thpoll83/PolyKybd/RoHS/PolyKybd-PCB-Layers.pdf

# PolyKybd Split72

## PCB Layer Documentation — Rev 3.2

Fabrication layer plots for the left and right boards (4-layer PCB), generated from the released production Gerber set.

### Prepared: 2026-07-13

PolyKybd — CE Technical File | PCB Layer Documentation
PCB Layer Documentation | Page 1

# Contents

## Left board (182.1 x 129.1 mm)

Top Copper — F.Cu p.4
Inner Layer 1 — In1.Cu p.5
Inner Layer 2 — In2.Cu p.6
Bottom Copper — B.Cu p.7
Top Solder Mask — F.Mask p.8 Bottom Solder Mask — B.Mask p.9 Top Paste — F.Paste p.10
Bottom Paste — B.Paste p.11
Board Outline — Edge.Cuts p.12

## Right board (182.1 x 129.1 mm)

Top Copper — F.Cu p.13
Inner Layer 1 — In1.Cu p.14
Inner Layer 2 — In2.Cu p.15
Bottom Copper — B.Cu p.16
Top Solder Mask — F.Mask p.17 Bottom Solder Mask — B.Mask p.18 Top Paste — F.Paste p.19
Bottom Paste — B.Paste p.20 Board Outline — Edge.Cuts p.21

# PCB construction summary

Layer count: 4 (2 outer + 2 inner copper). Stack order top->bottom: F.Cu, In1.Cu, In2.Cu, B.Cu. Base material: FR-4. Surface finish: ENIG or lead-free HASL (per PCB fabricator RoHS certificate). Left board outline: 182.1 x 129.1 mm.
Right board outline: 182.1 x 129.1 mm.

Layers shown: copper (x4), solder mask (top/bottom), solder paste (top/bottom), board outline. Silkscreen layers are part of the released Gerber set; export from KiCad (kicad-cli) if required.
Confirm exact dielectric thicknesses / copper weights with the PCB fabricator.

# Left board — Top Copper — F.Cu

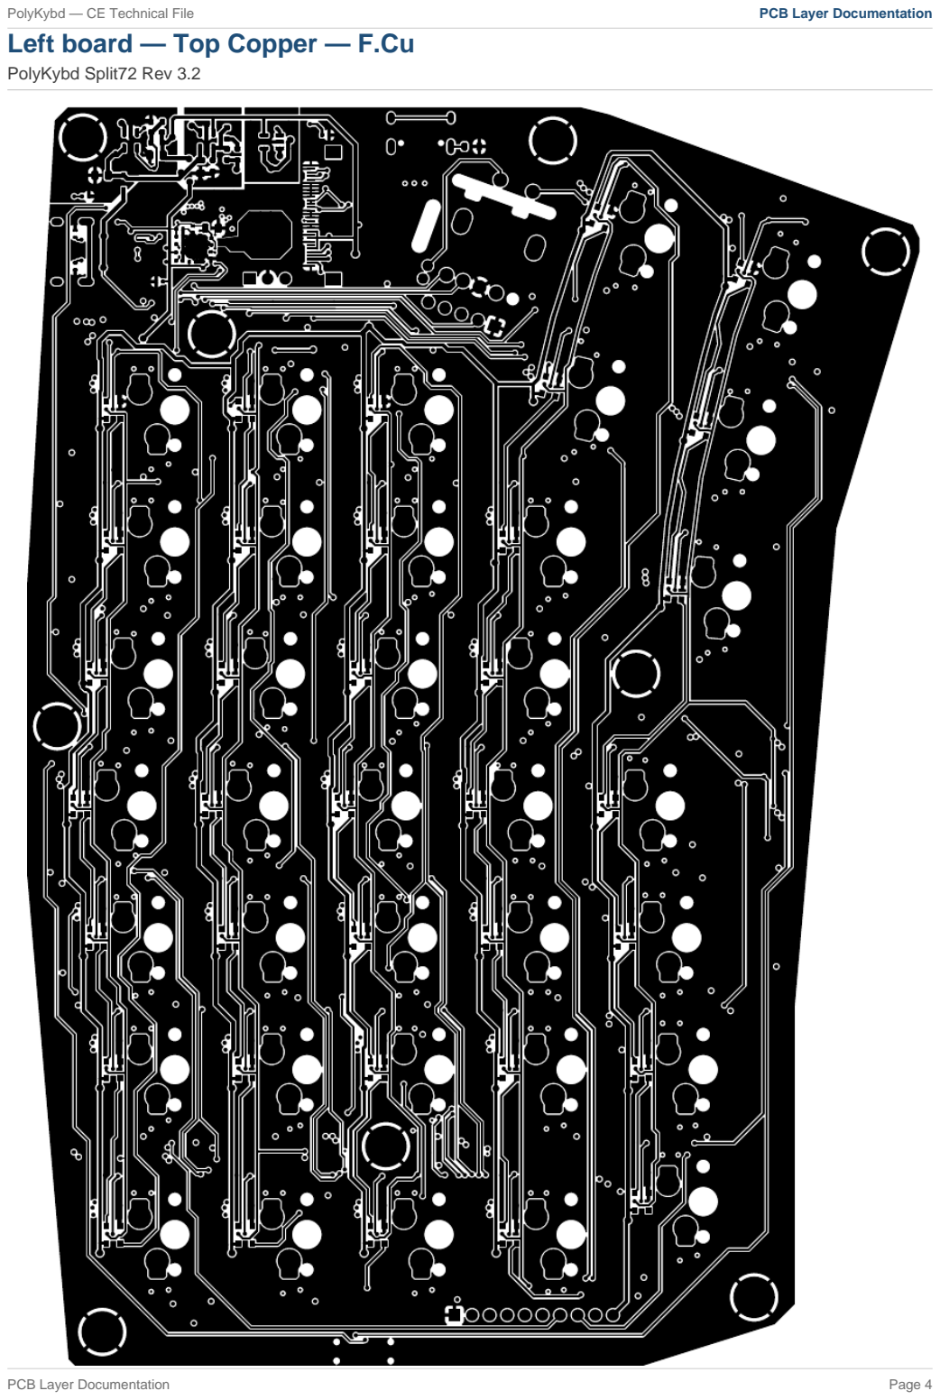
[picture p49: page 4]

### PolyKybd Split72 Rev 3.2

# Left board — Inner Layer 1 — In1.Cu

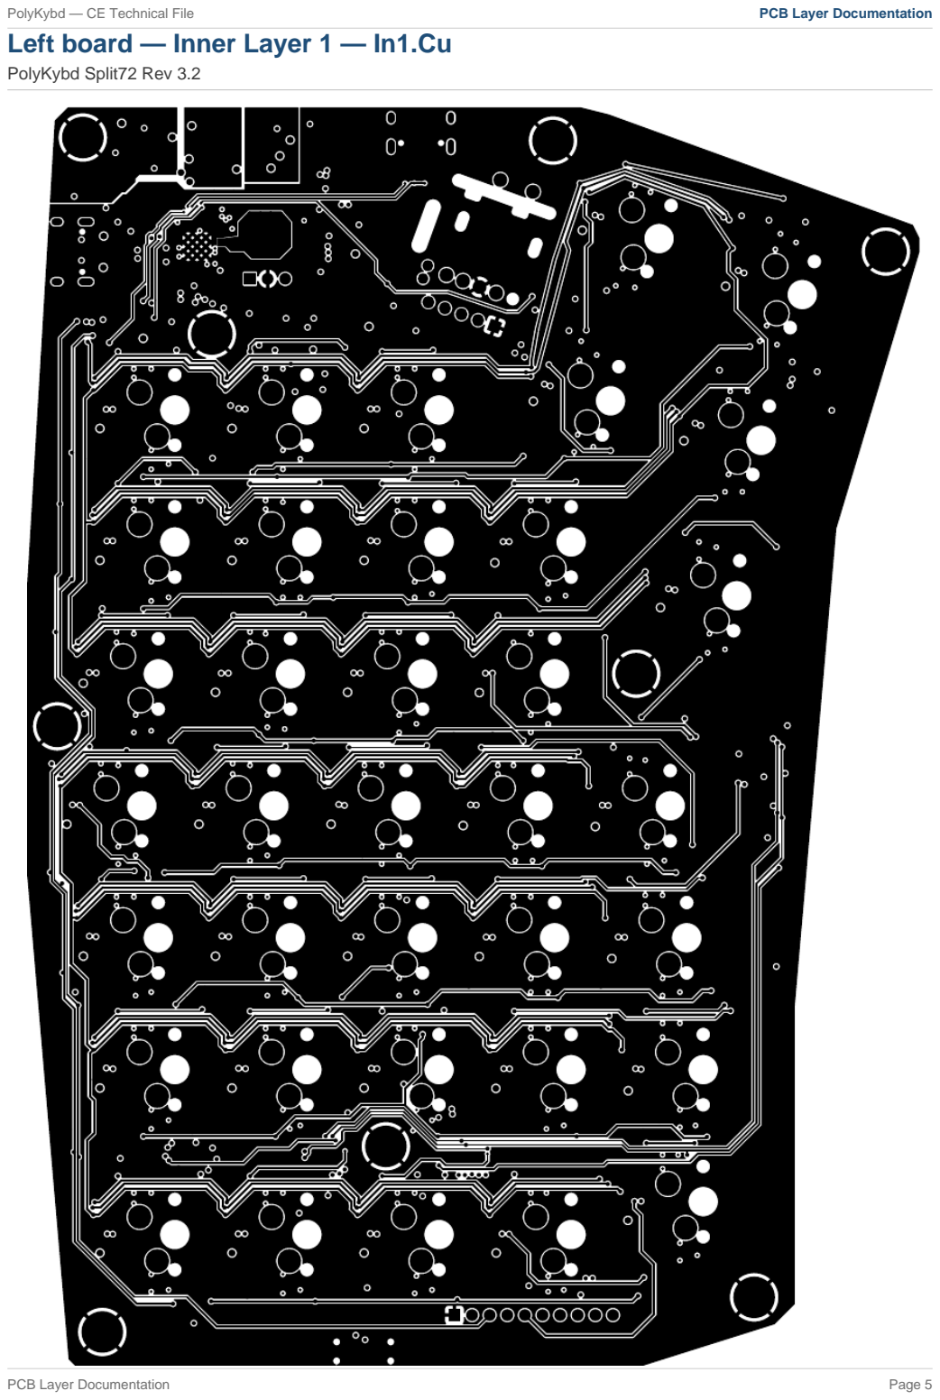
[picture p50: page 5]

# Left board — Inner Layer 2 — In2.Cu

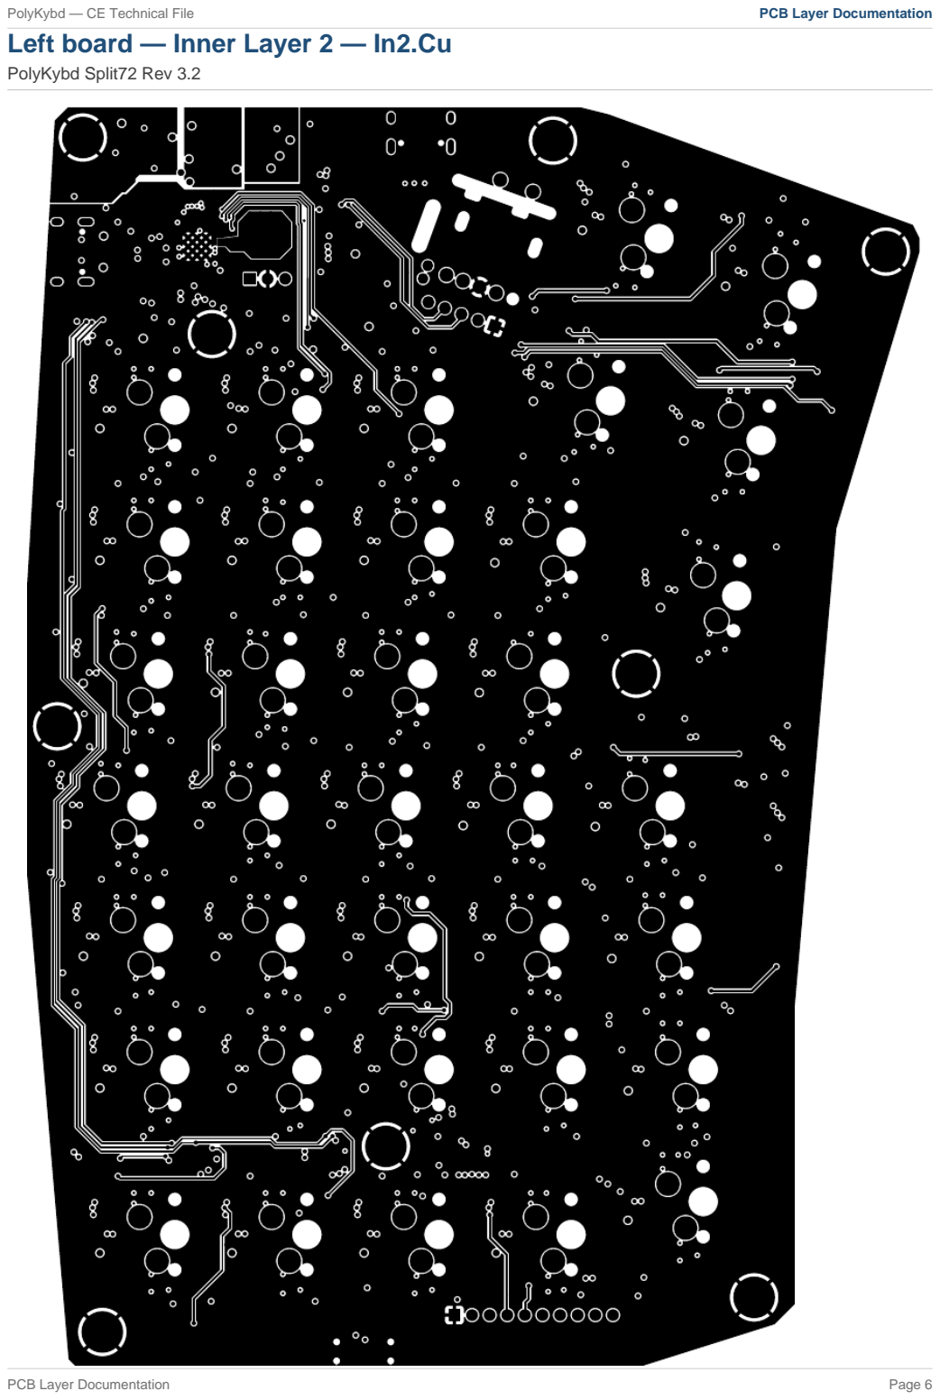
[picture p51: page 6]

# Left board — Bottom Copper — B.Cu

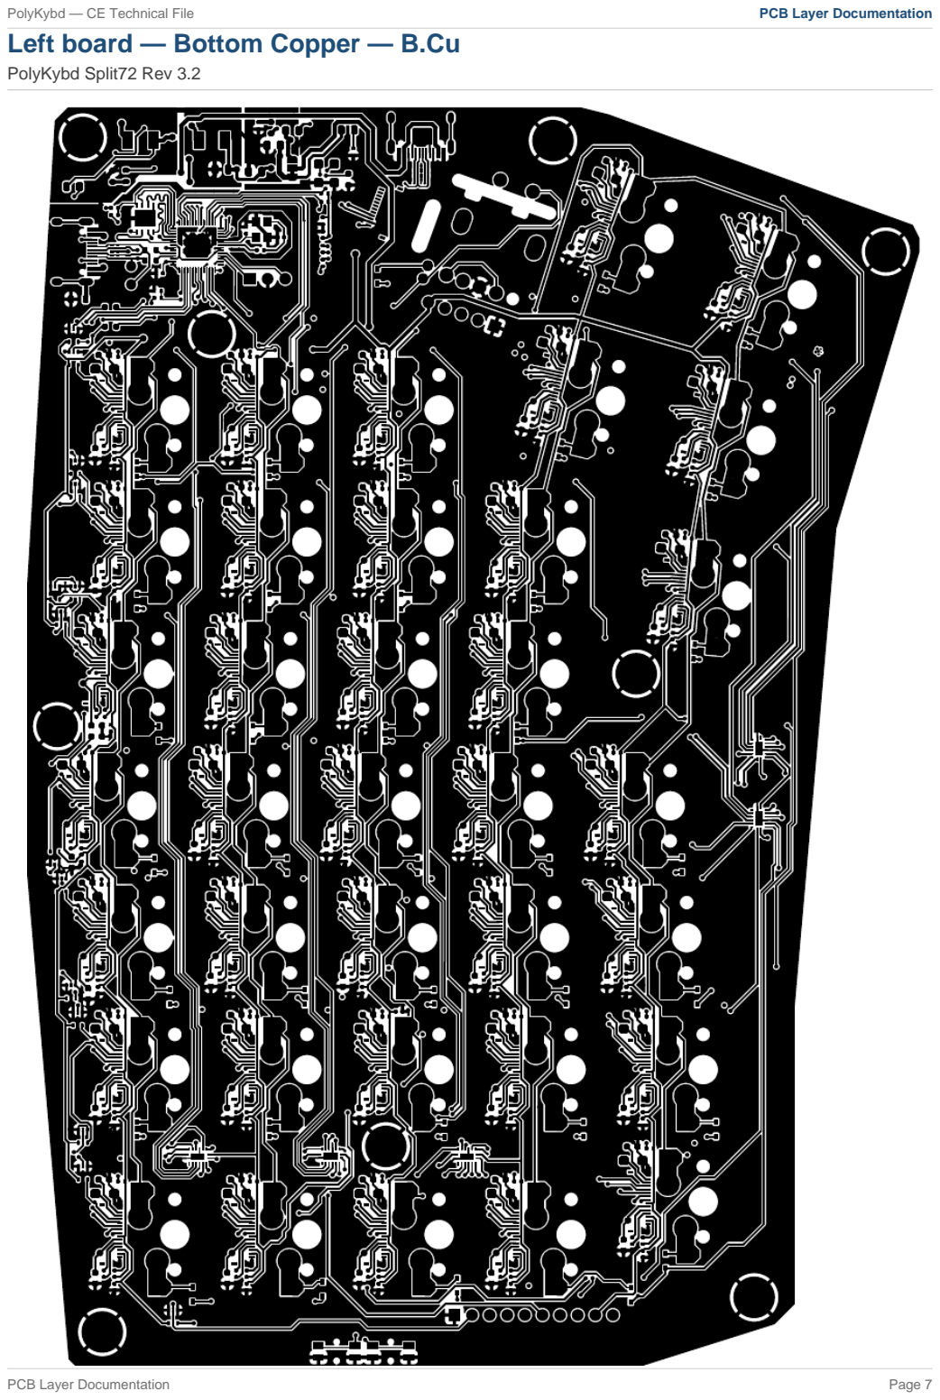
[picture p52: page 7]

# Left board — Top Solder Mask — F.Mask

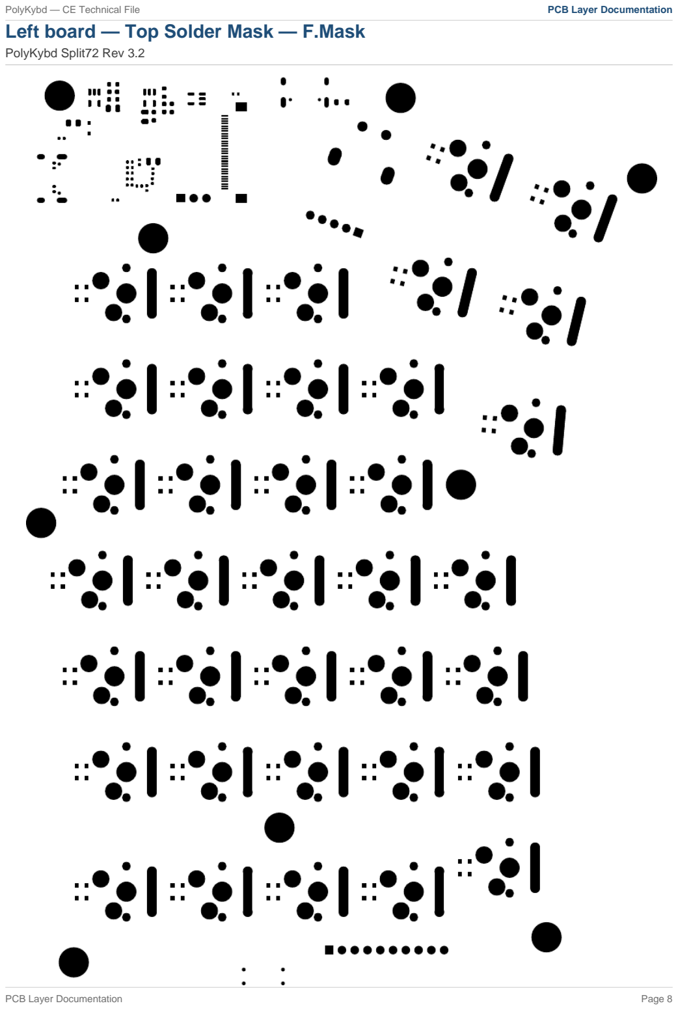
[picture p53: page 8]

# Left board — Bottom Solder Mask — B.Mask

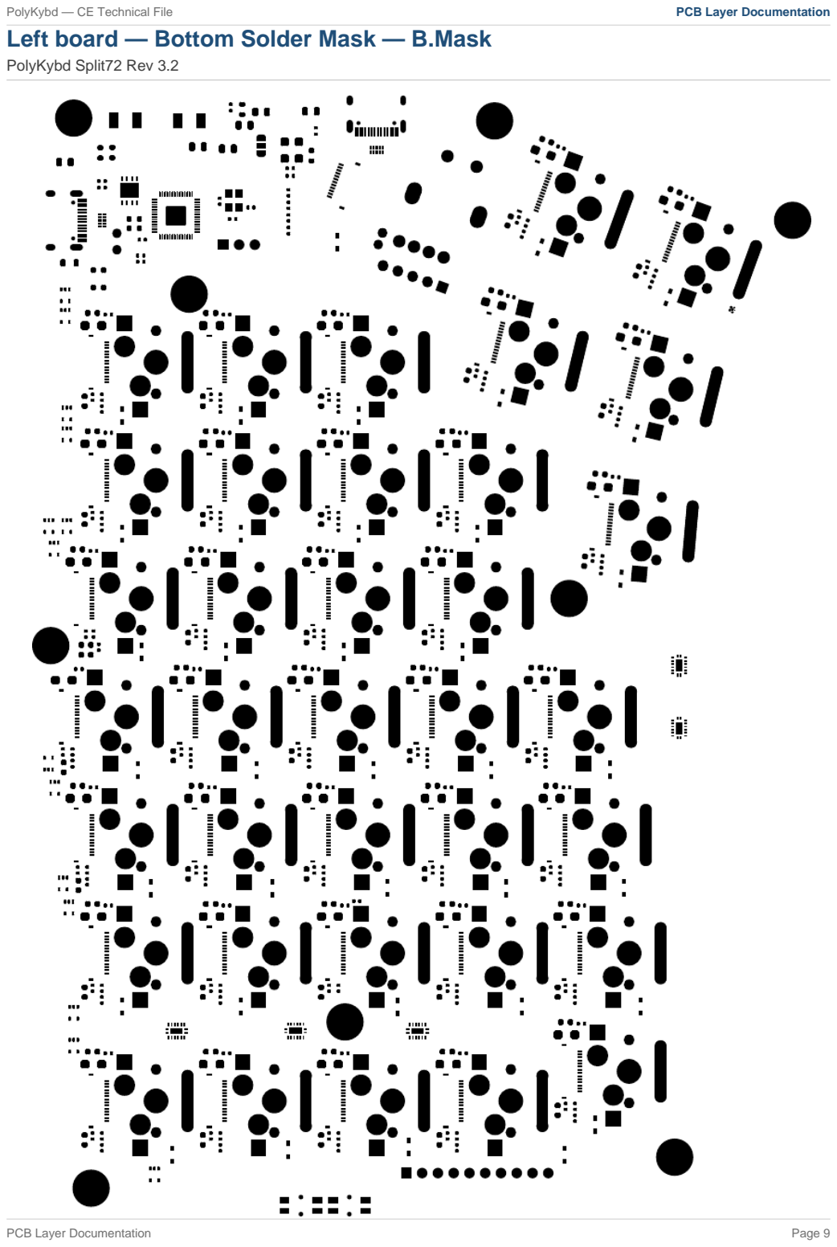
[picture p54: page 9]

# Left board — Top Paste — F.Paste

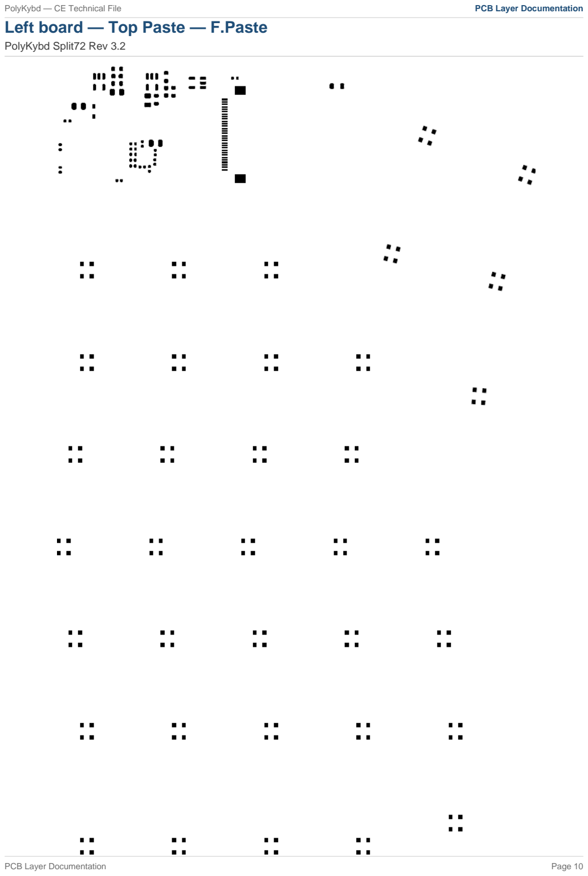
[picture p55: page 10]

# Left board — Bottom Paste — B.Paste

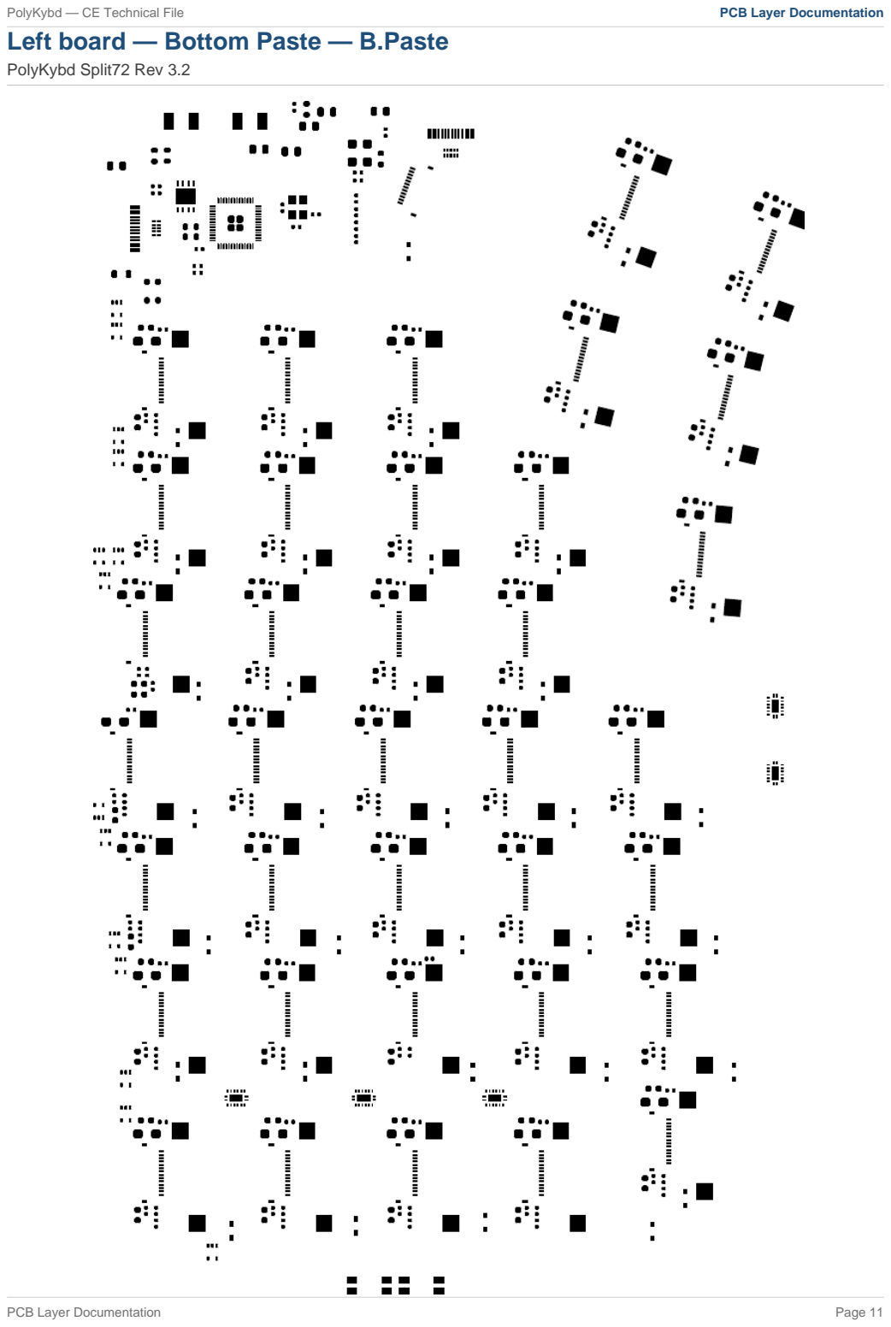
[picture p56: page 11]

# Left board — Board Outline — Edge.Cuts

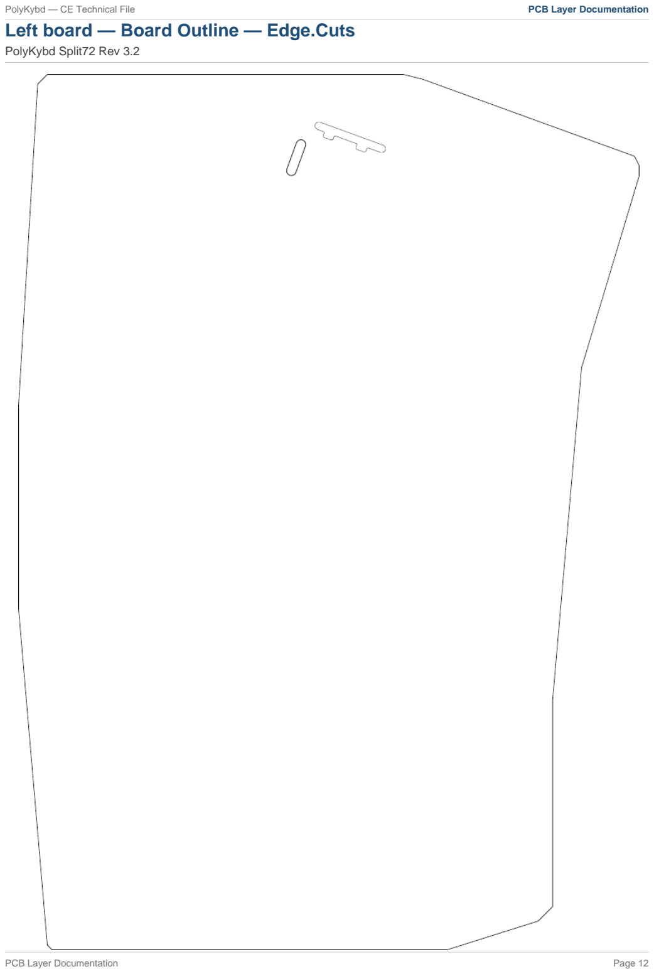
[picture p57: page 12]

# Right board — Top Copper — F.Cu

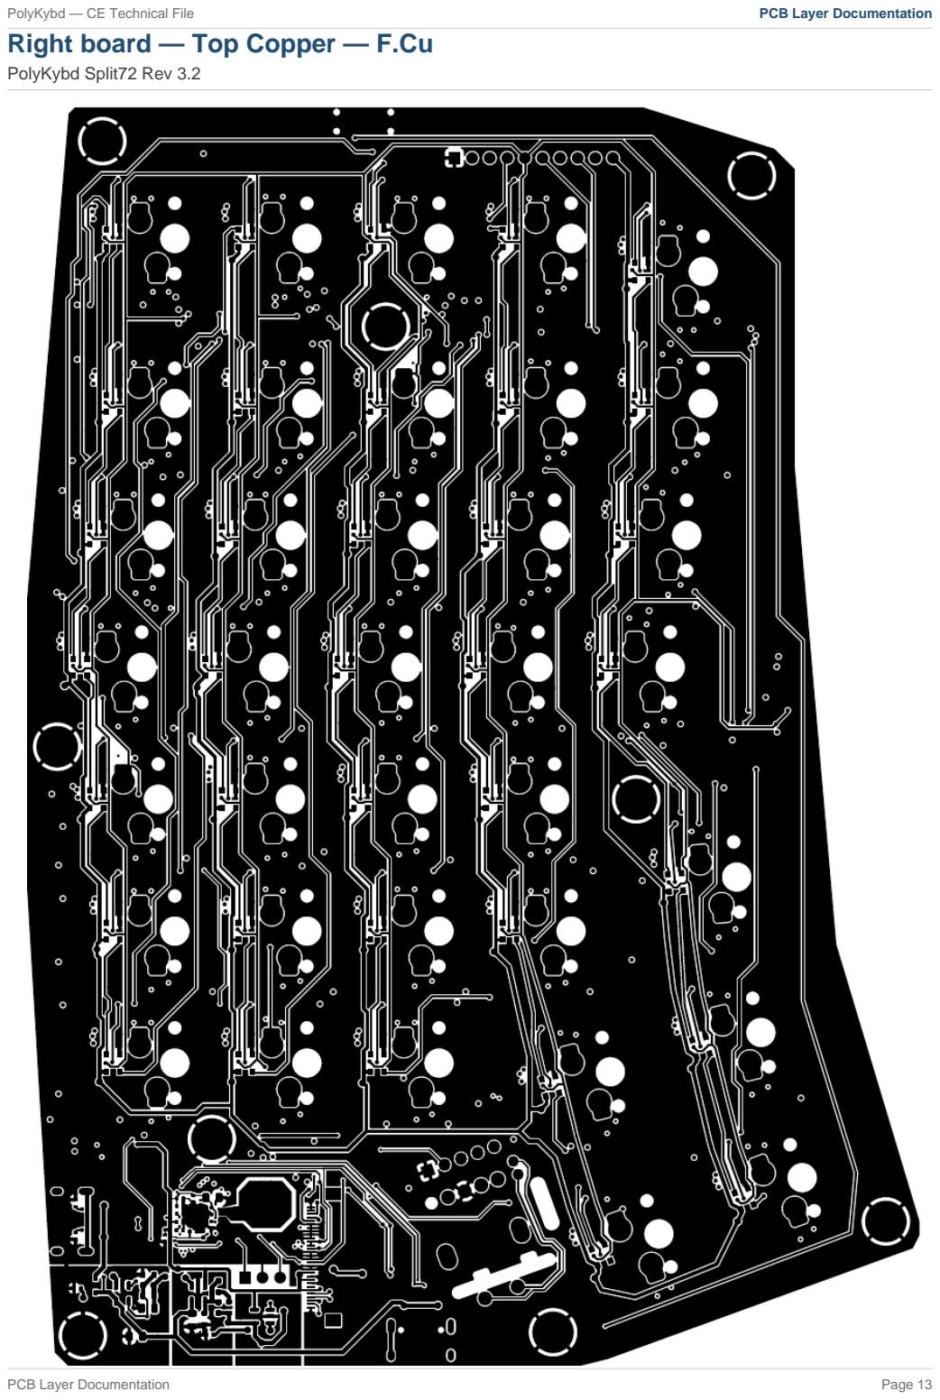
[picture p58: page 13]

# Right board — Inner Layer 1 — In1.Cu

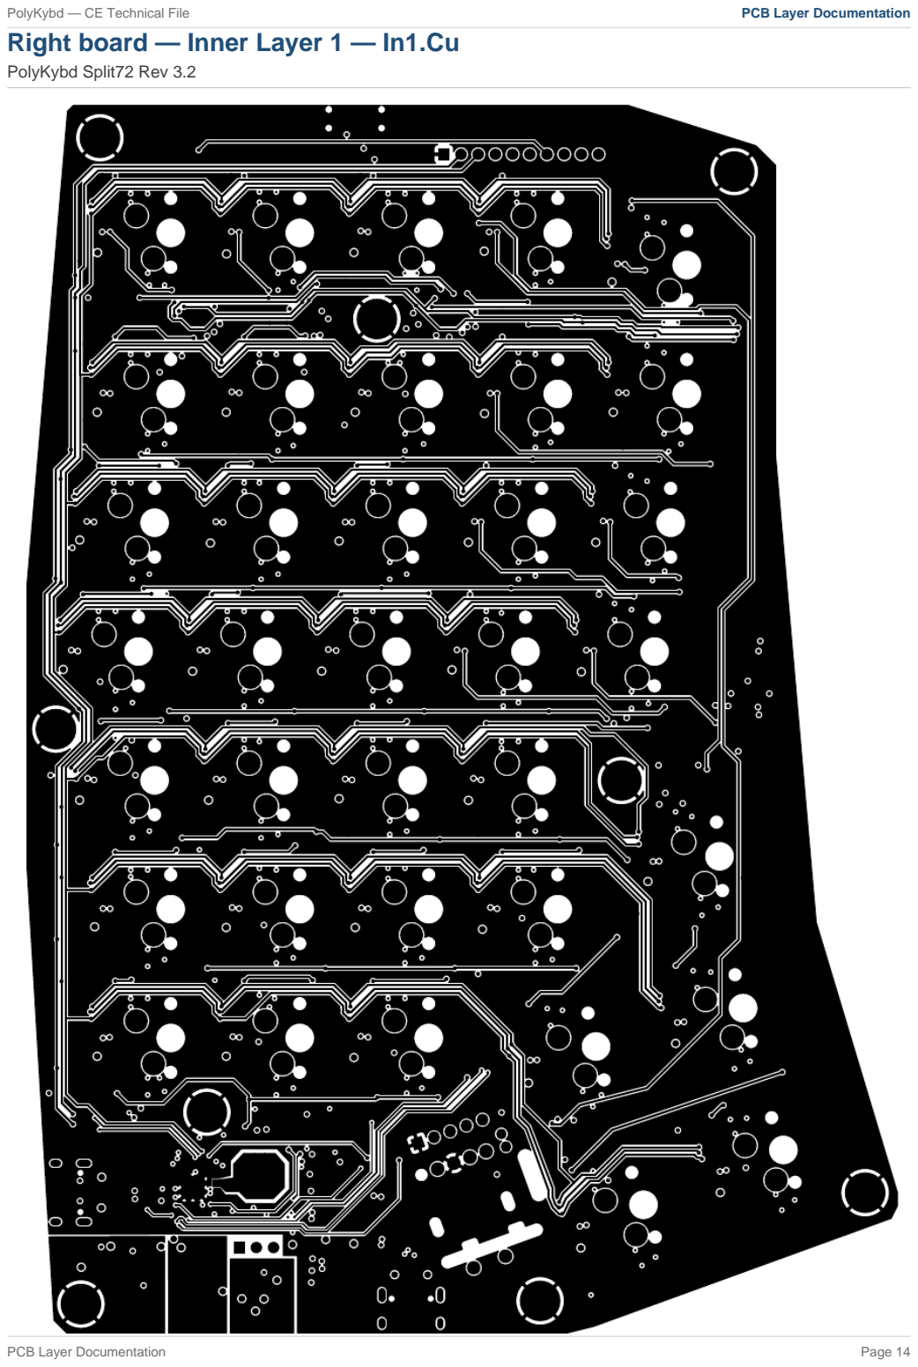
[picture p59: page 14]

# Right board — Inner Layer 2 — In2.Cu

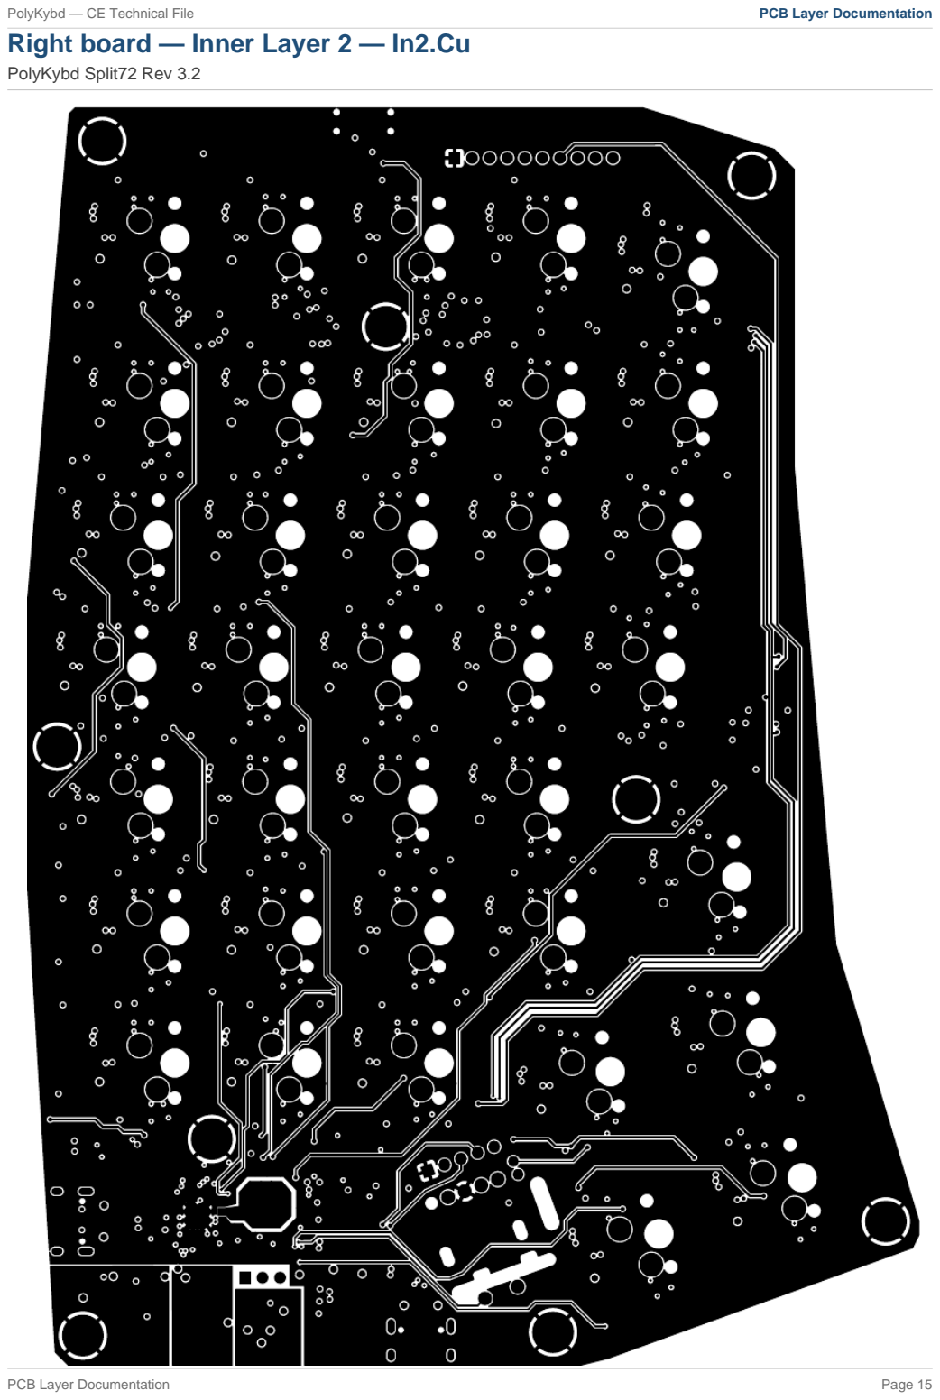
[picture p60: page 15]

# Right board — Bottom Copper — B.Cu

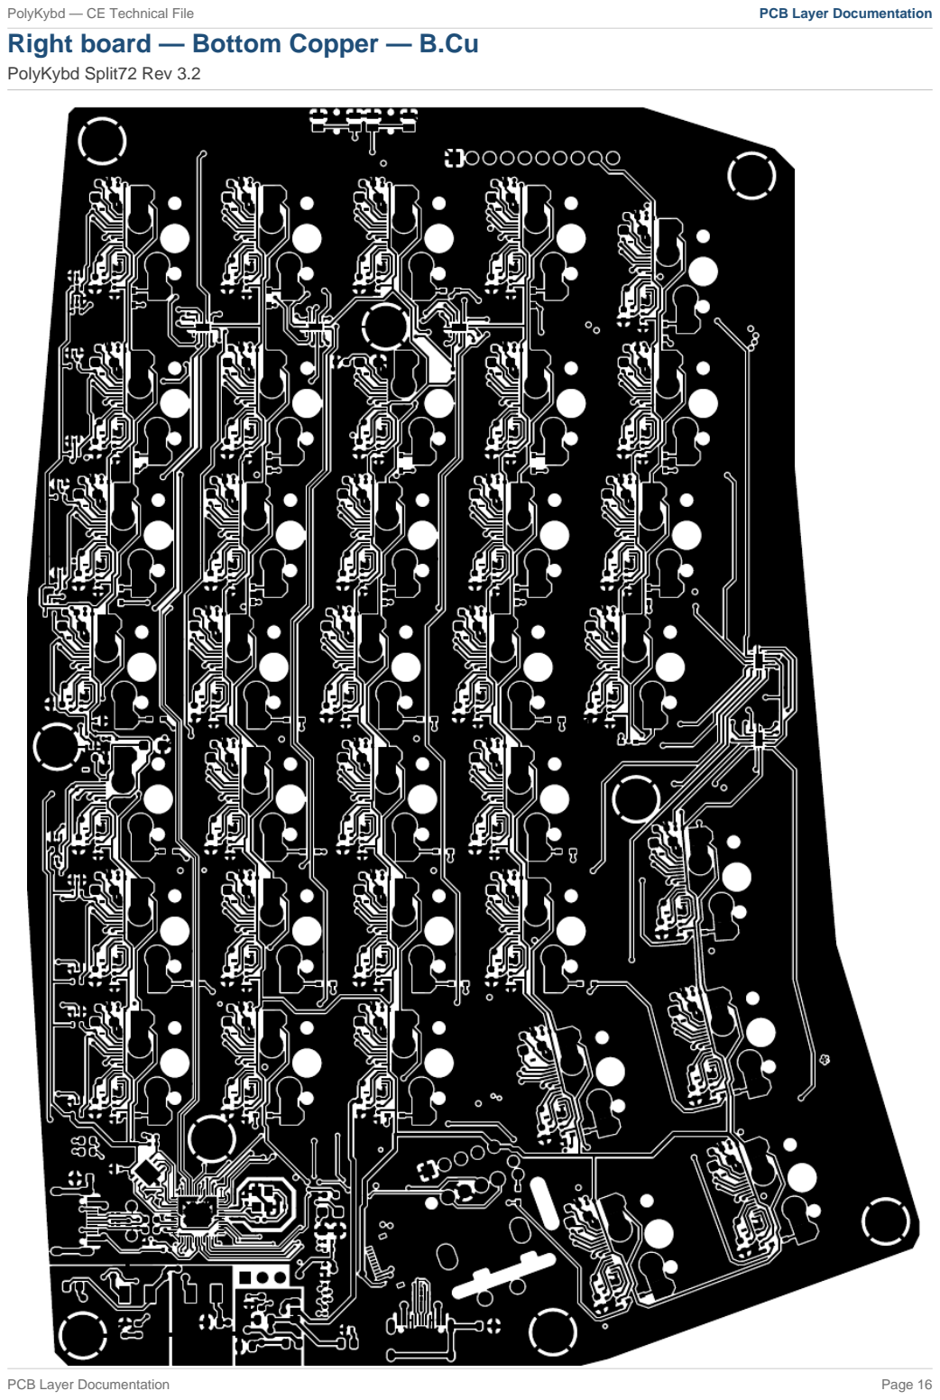
[picture p61: page 16]

# Right board — Top Solder Mask — F.Mask

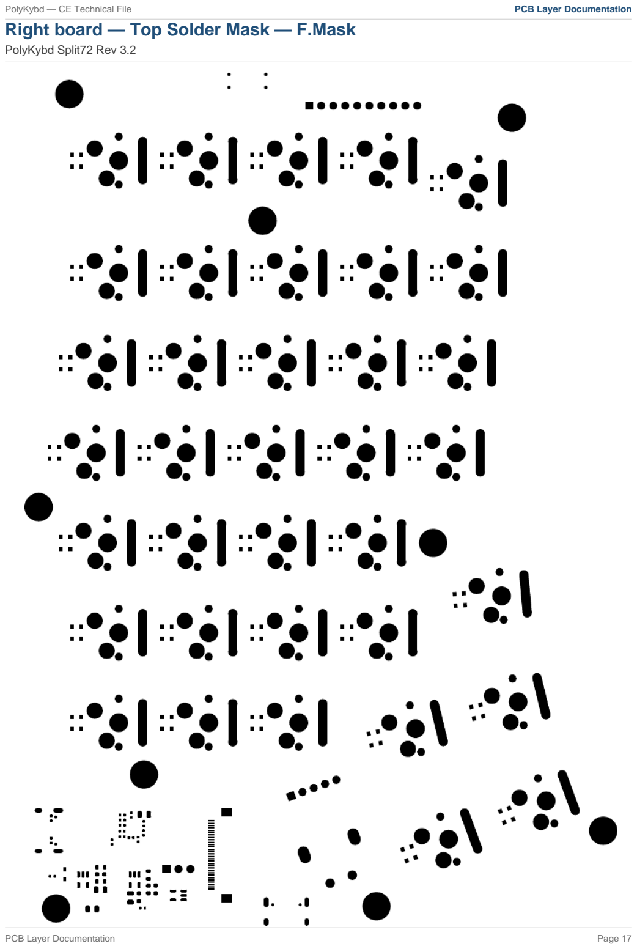
[picture p62: page 17]

# Right board — Bottom Solder Mask — B.Mask

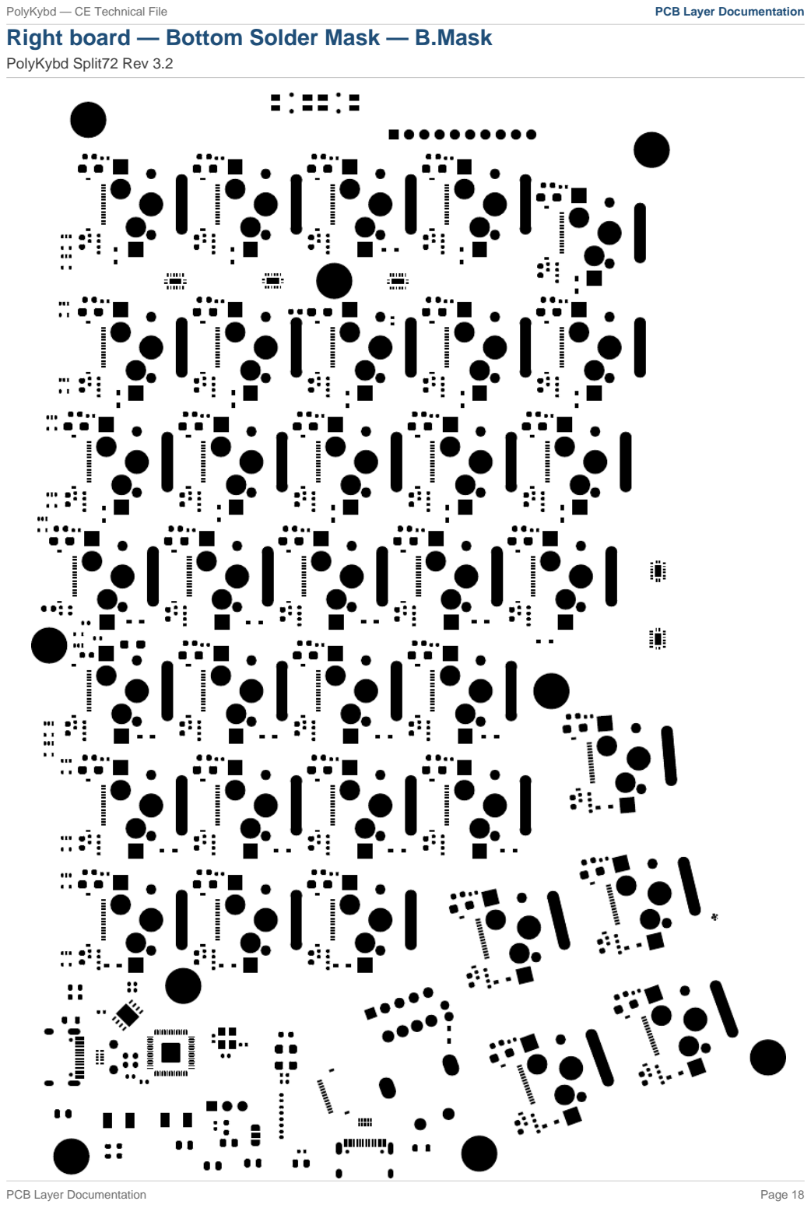
[picture p63: page 18]

# Right board — Top Paste — F.Paste

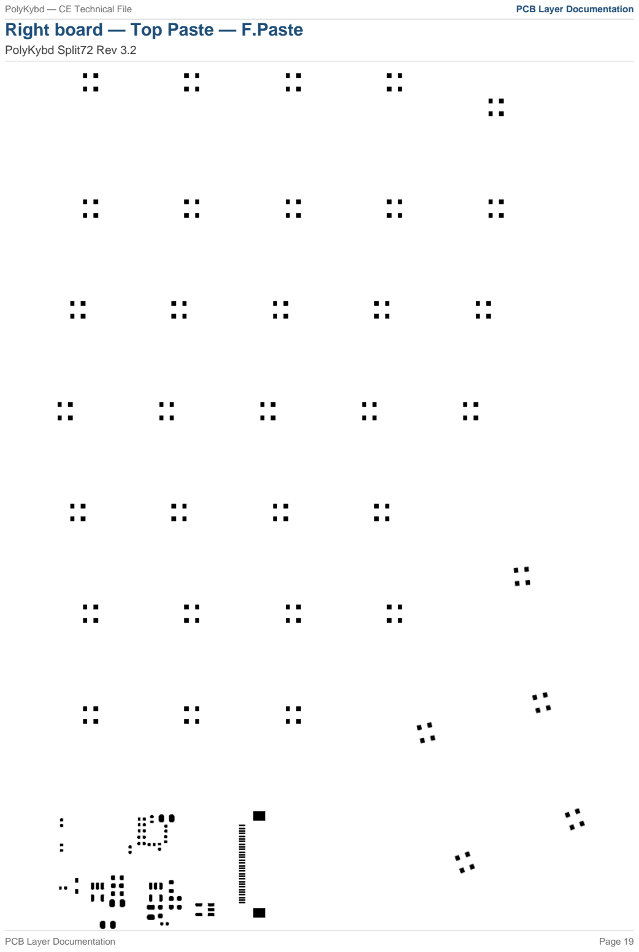
[picture p64: page 19]

# Right board — Bottom Paste — B.Paste

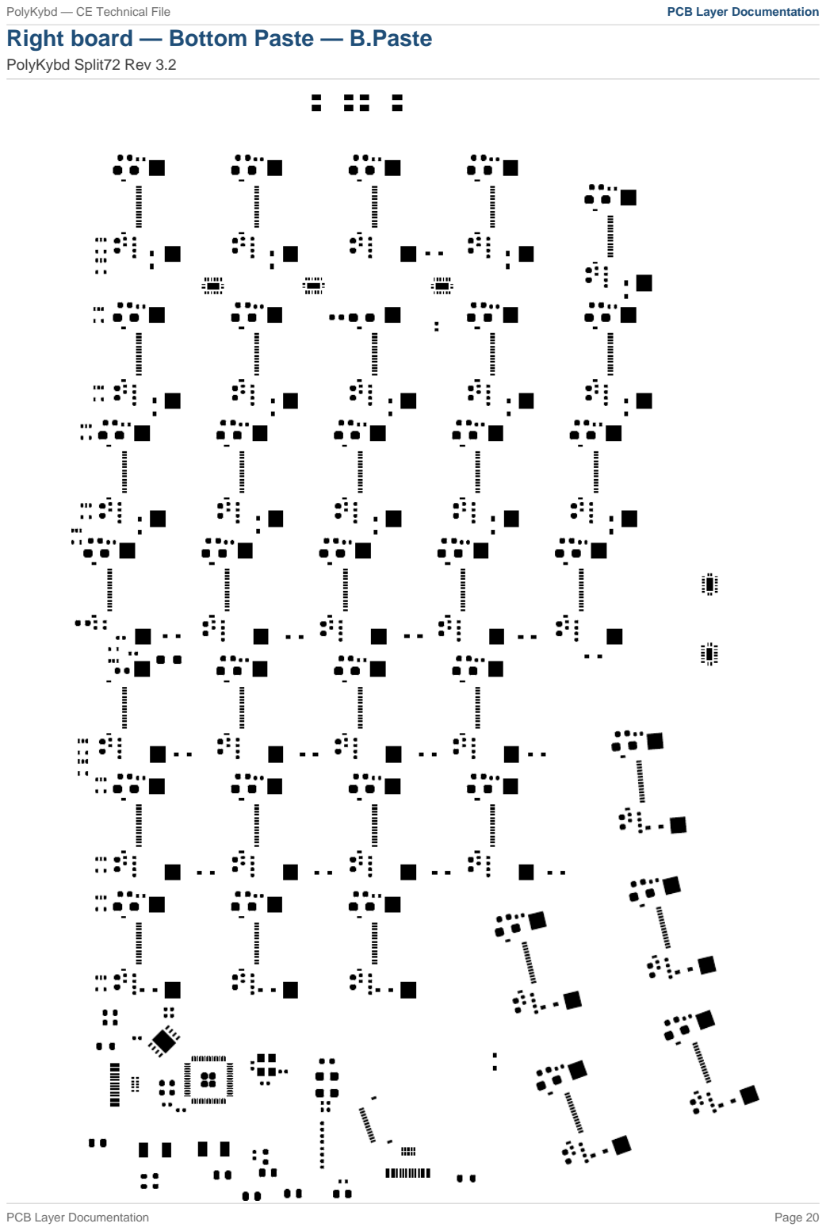
[picture p65: page 20]

# Right board — Board Outline — Edge.Cuts

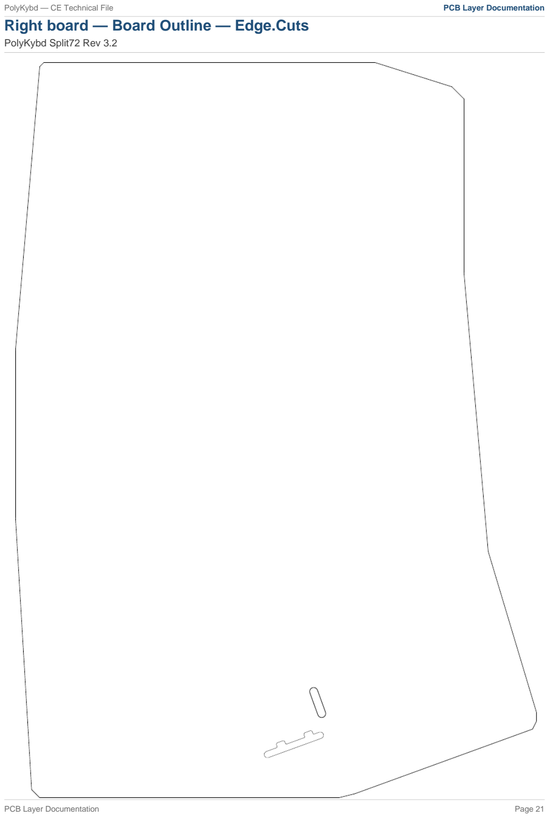
[picture p66: page 21]
