thpoll83/PolyKybd/RoHS/2006180000_BOYAMICRO-BY25Q64ESCIG-R_C50176394.pdf

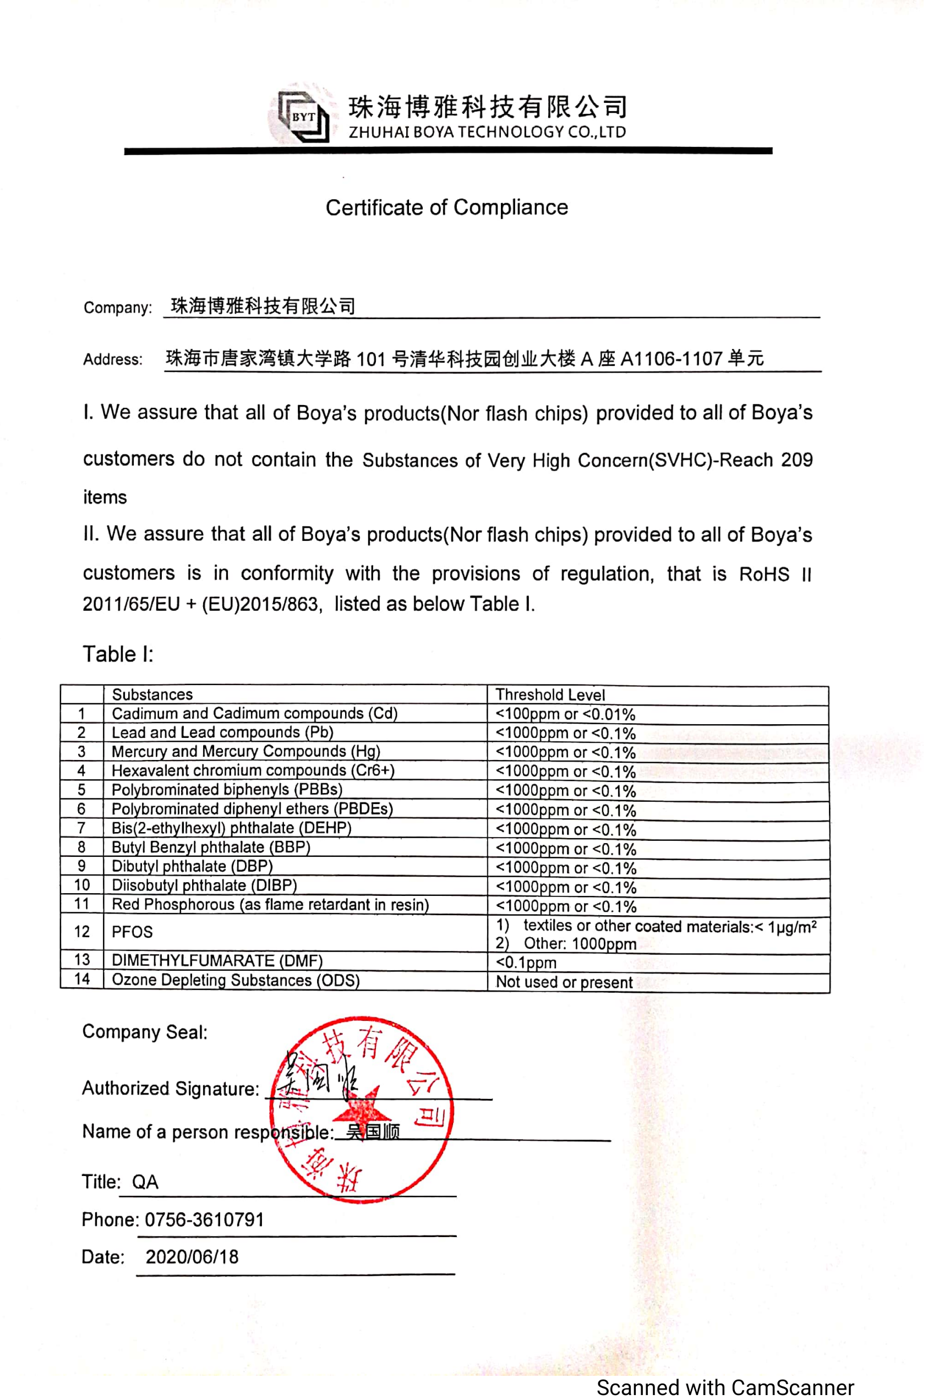
[picture p67: page 1]
