thpoll83/PolyKybd/RoHS/vishay-rohs-20250901.pdf

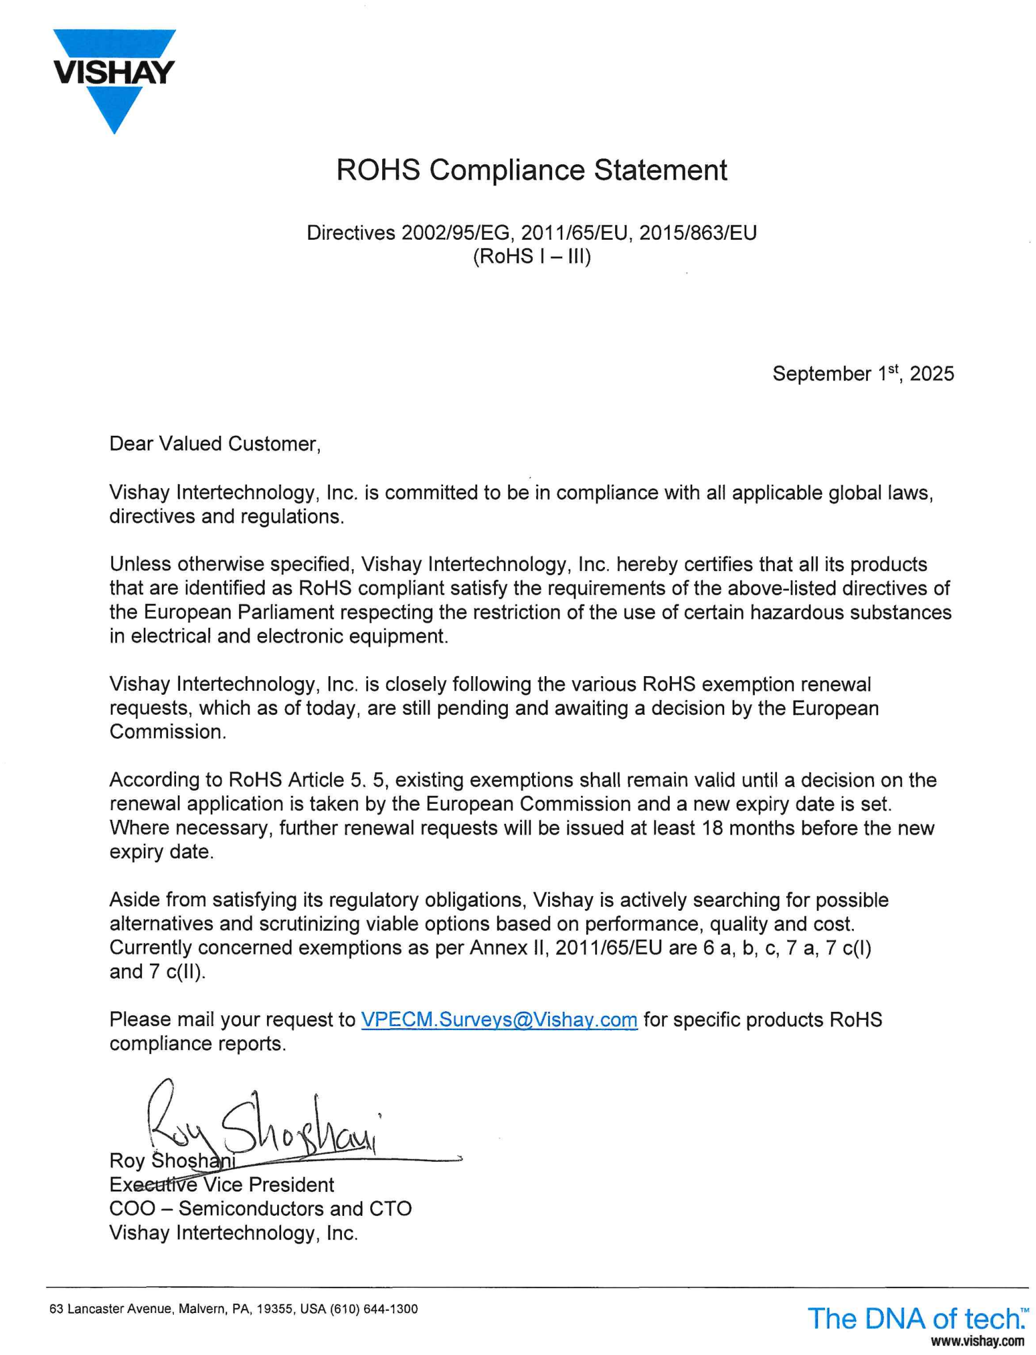
[picture p68: page 1]
