thpoll83/PolyKybd/RoHS/rp2040-rohs.pdf

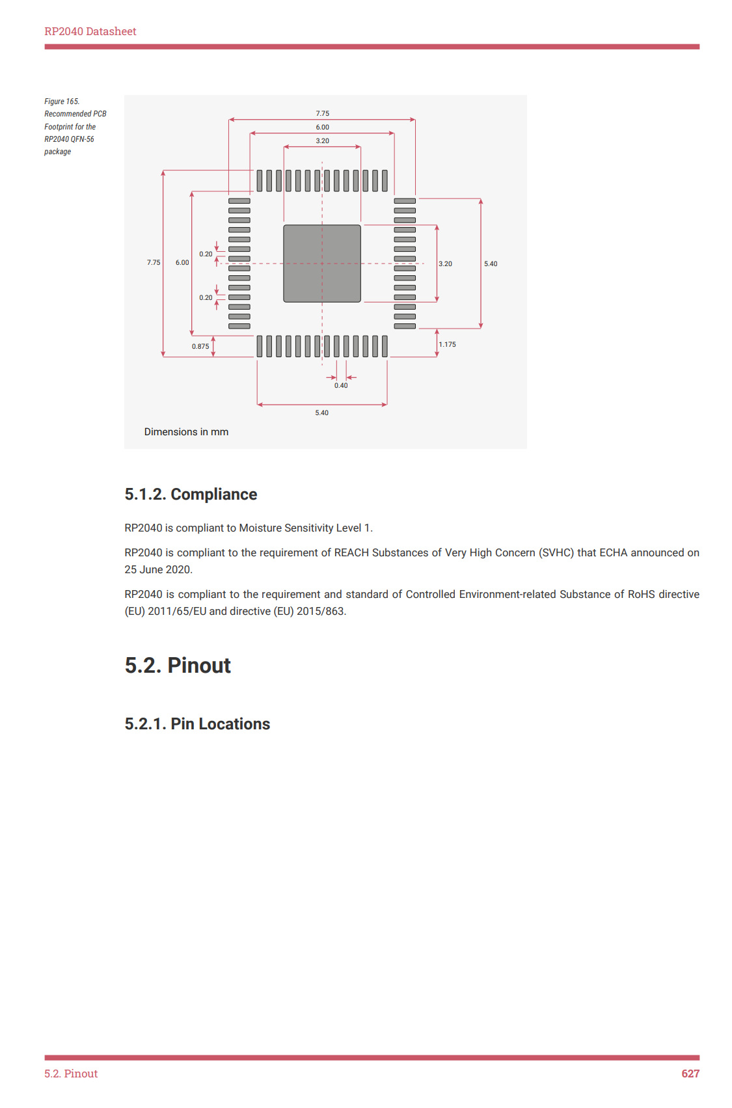
[picture p69: page 1]
