thpoll83/PolyKybd/RoHS/winbond-W25Q64JV-rohs.pdf

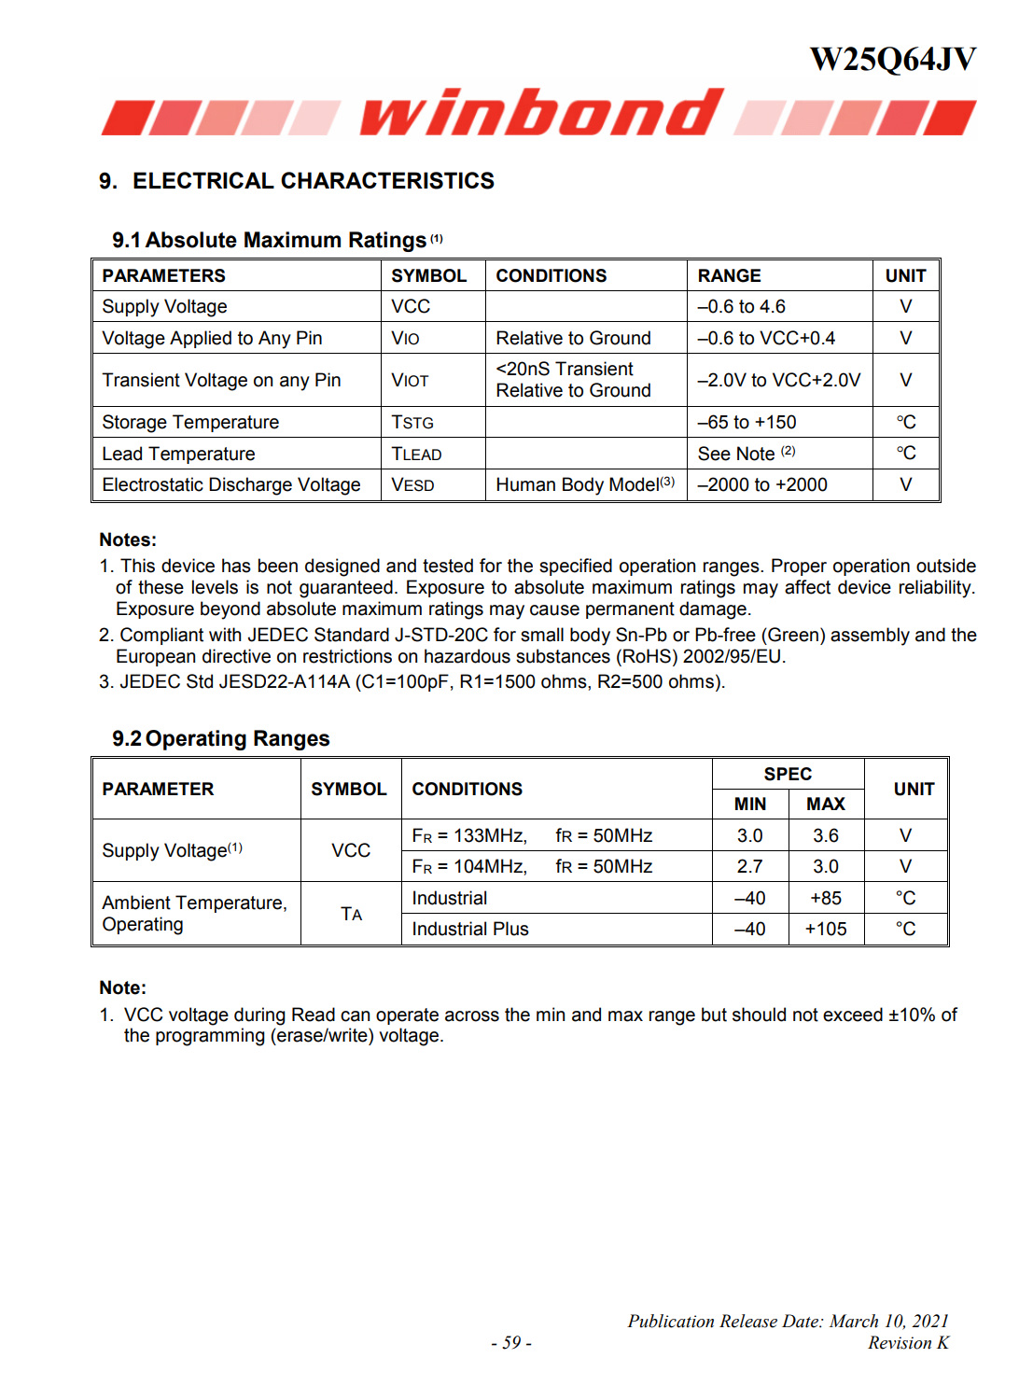
[picture p70: page 1]
