thpoll83/PolyKybd/RoHS/fh-iso14001.pdf

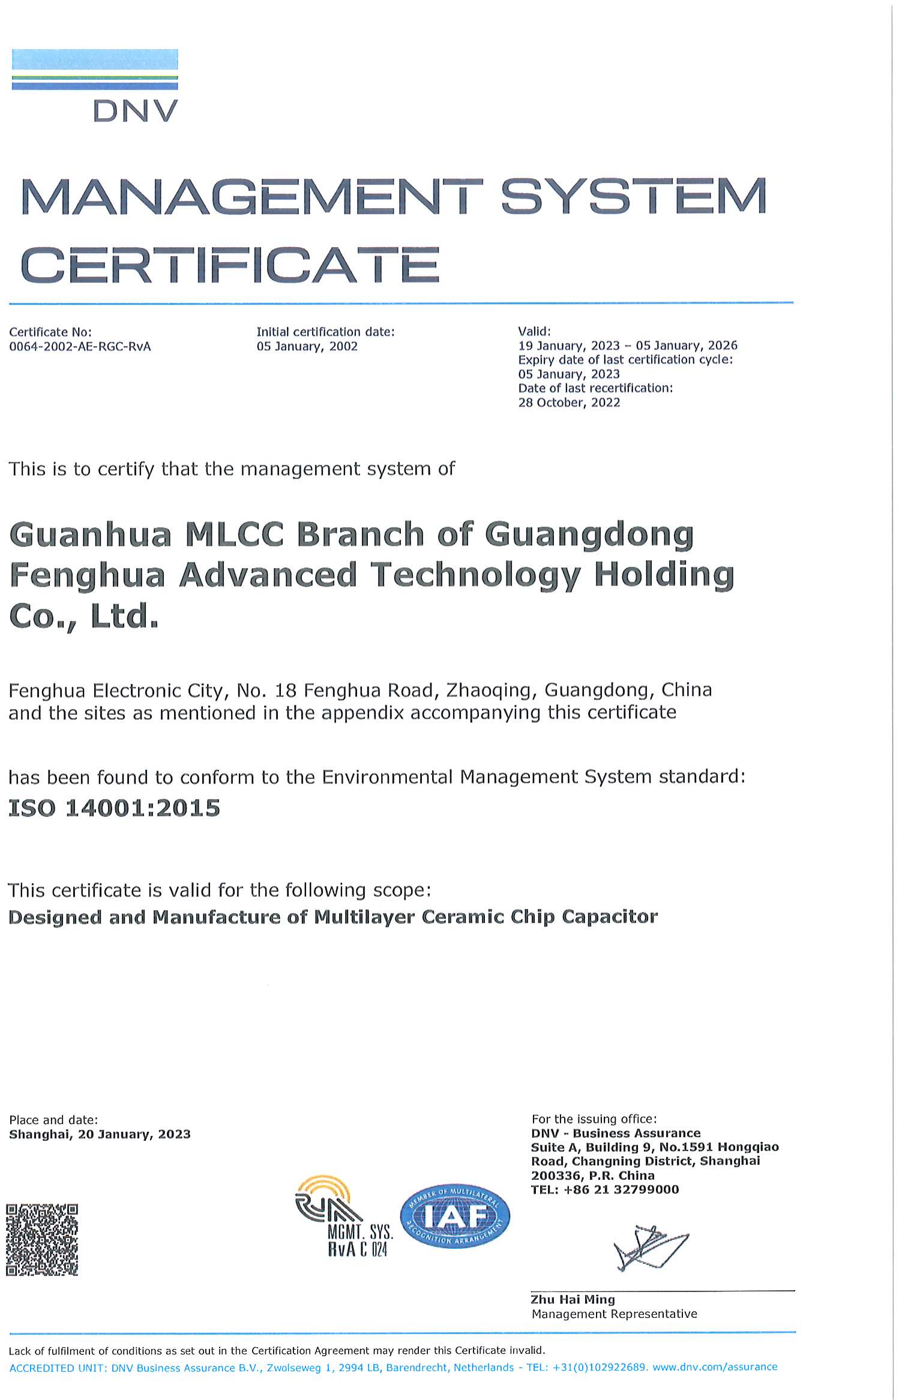
[picture p71: page 1]
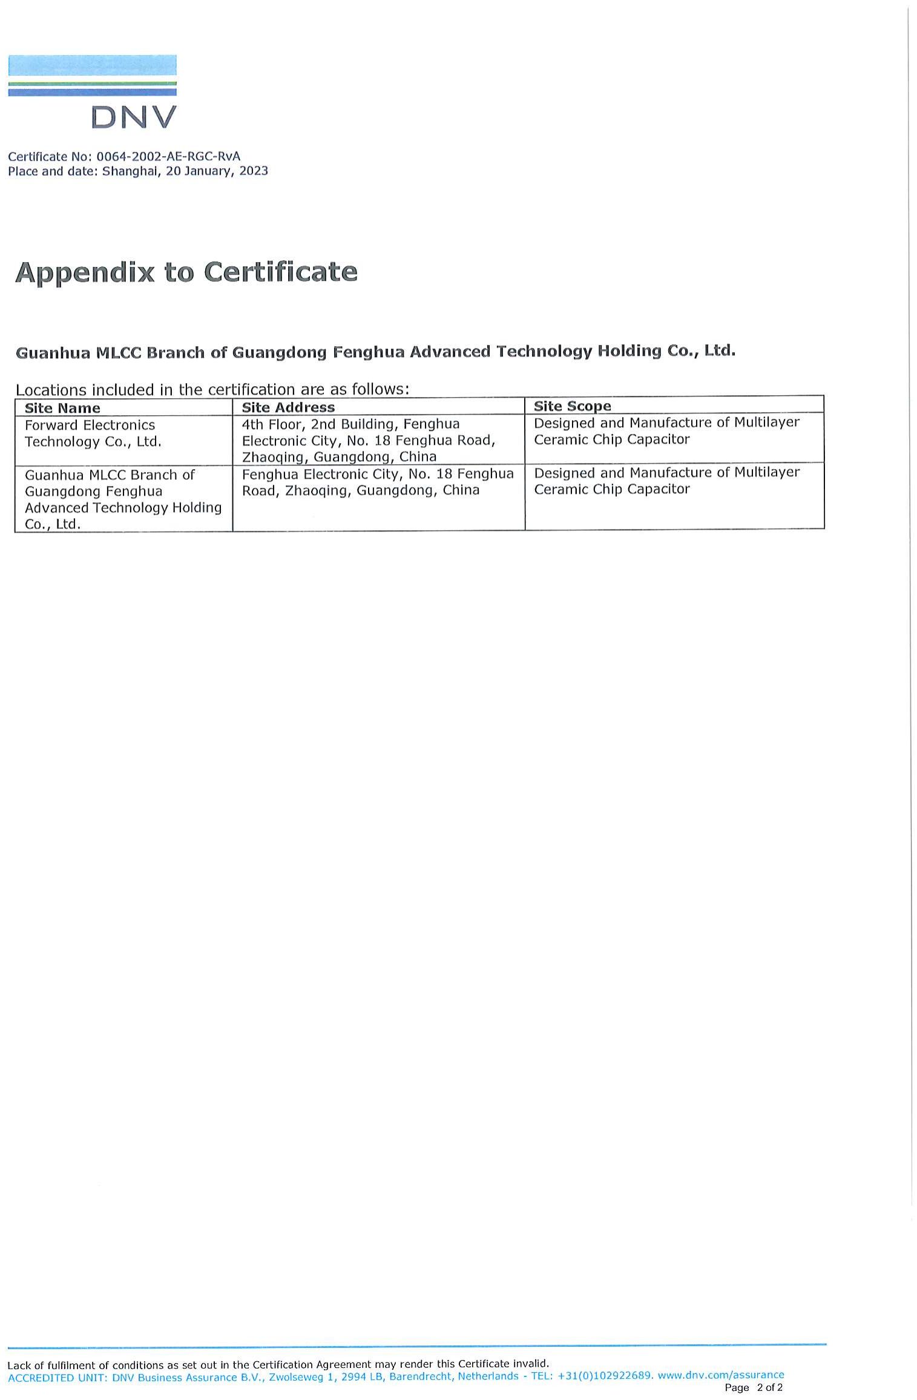
[picture p72: page 2]
