thpoll83/PolyKybd/felt_case.jpg

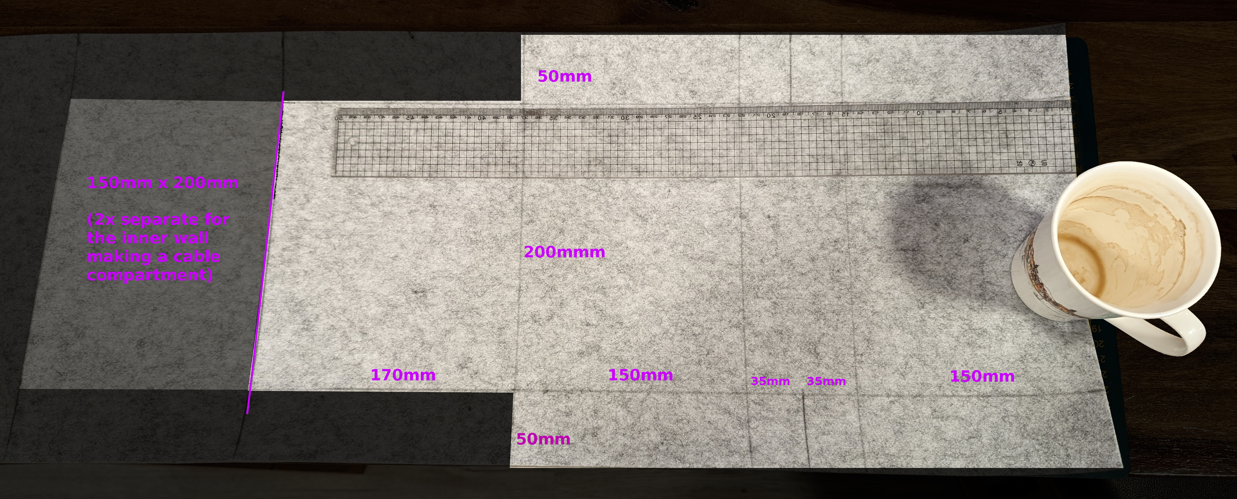
felt_case.jpg
