thpoll83/PolyKybd/images/high_res/display2.jpg

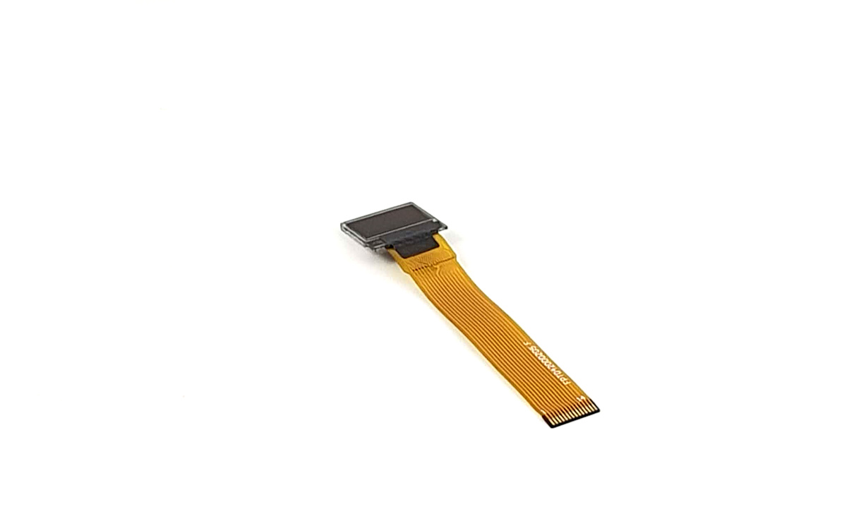
images/high_res/display2.jpg
