thpoll83/PolyKybd/images/high_res/display.jpg

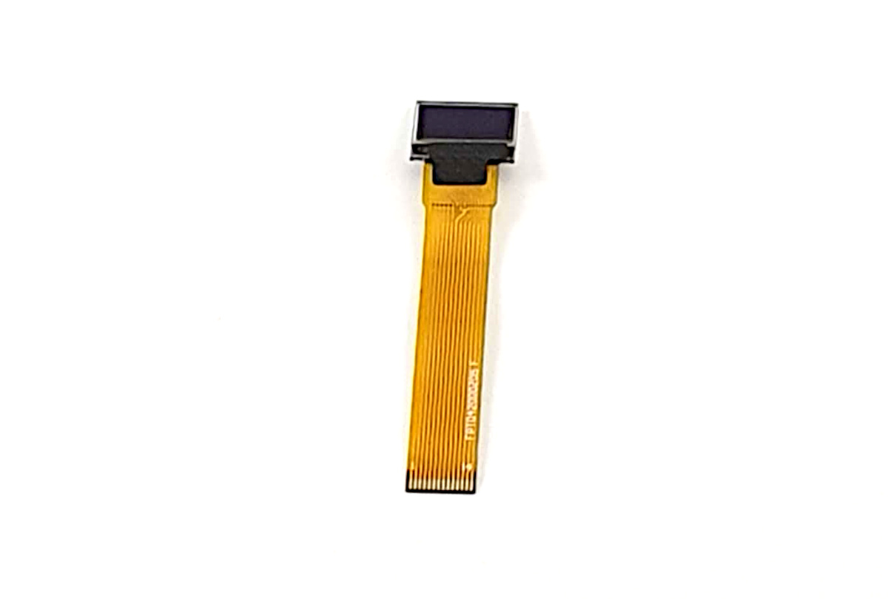
images/high_res/display.jpg
