thpoll83/PolyKybd/images/high_res/display_w_stem_cap.jpg

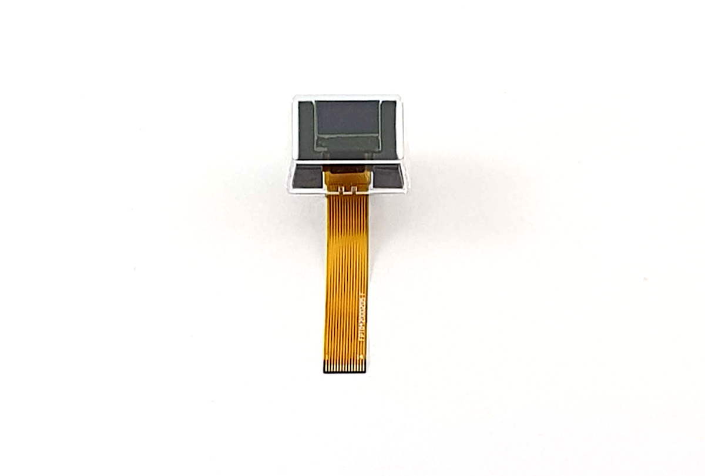
images/high_res/display_w_stem_cap.jpg
