thpoll83/PolyKybd/images/high_res/left_kb.jpg

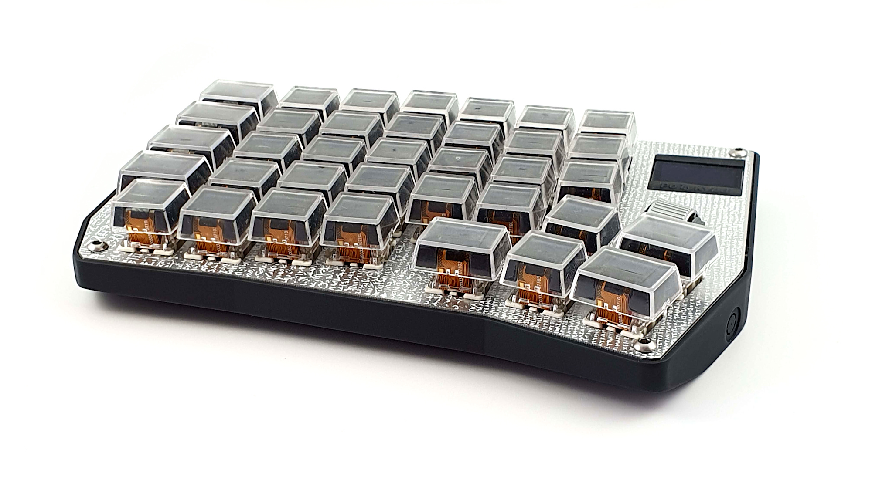
images/high_res/left_kb.jpg
