thpoll83/PolyKybd/images/high_res/left_pcb_r2.jpg

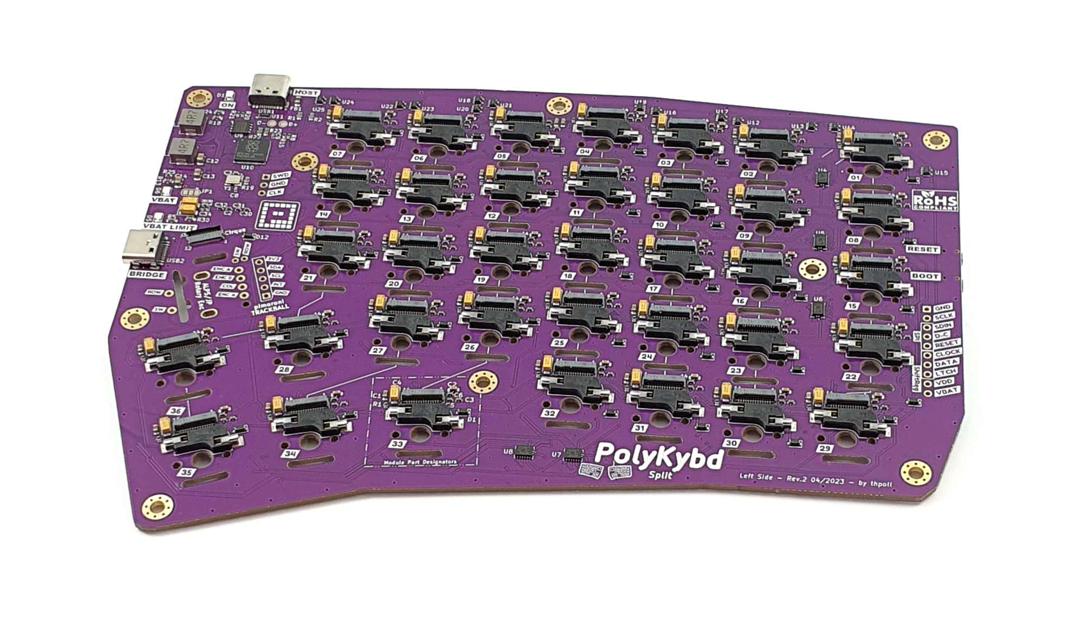
images/high_res/left_pcb_r2.jpg
