thpoll83/PolyKybd/images/high_res/left_plate.jpg

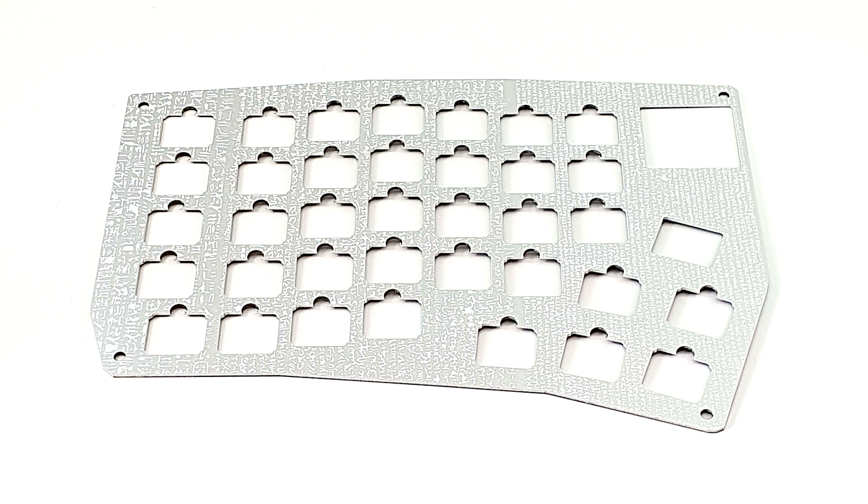
images/high_res/left_plate.jpg
