thpoll83/PolyKybd/images/high_res/right_without_caps_and_disp.jpg

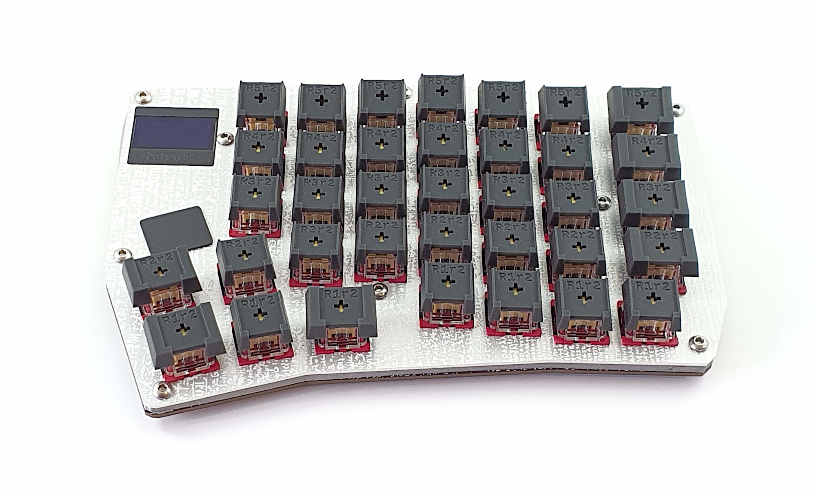
images/high_res/right_without_caps_and_disp.jpg
