thpoll83/PolyKybd/images/high_res/status_display2.jpg

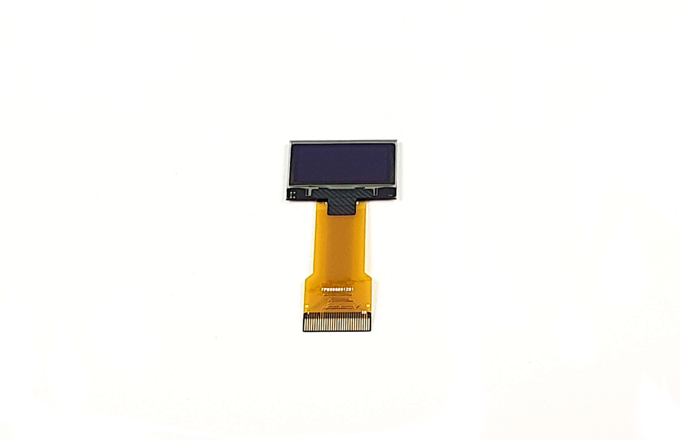
images/high_res/status_display2.jpg
