thpoll83/PolyKybd/images/high_res/status_display.jpg

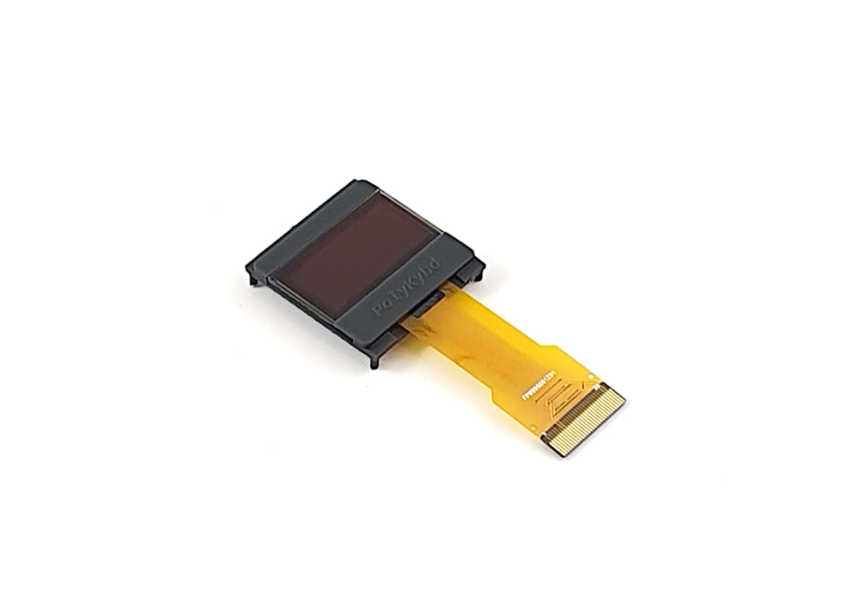
images/high_res/status_display.jpg
