thpoll83/PolyKybd/images/high_res/stem_1u25.jpg

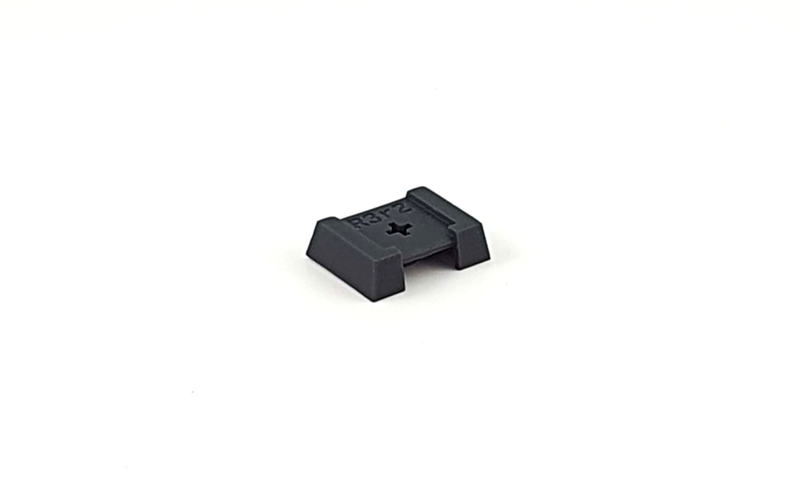
images/high_res/stem_1u25.jpg
