thpoll83/PolyKybd/images/high_res/trackpad.jpg

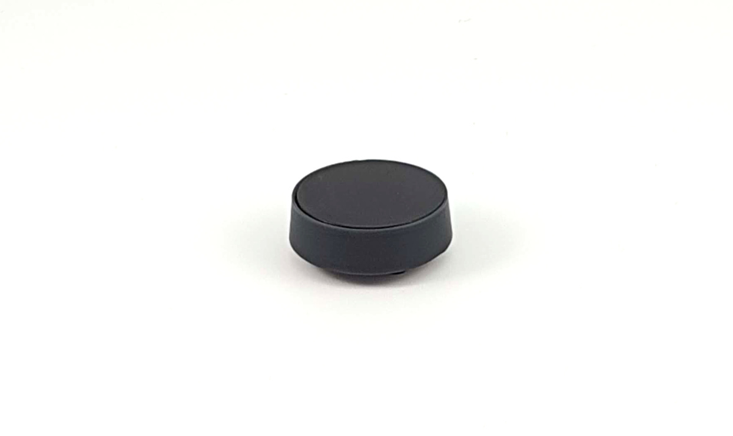
images/high_res/trackpad.jpg
