thpoll83/PolyKybd/images/PolyKybdSplit72.jpg

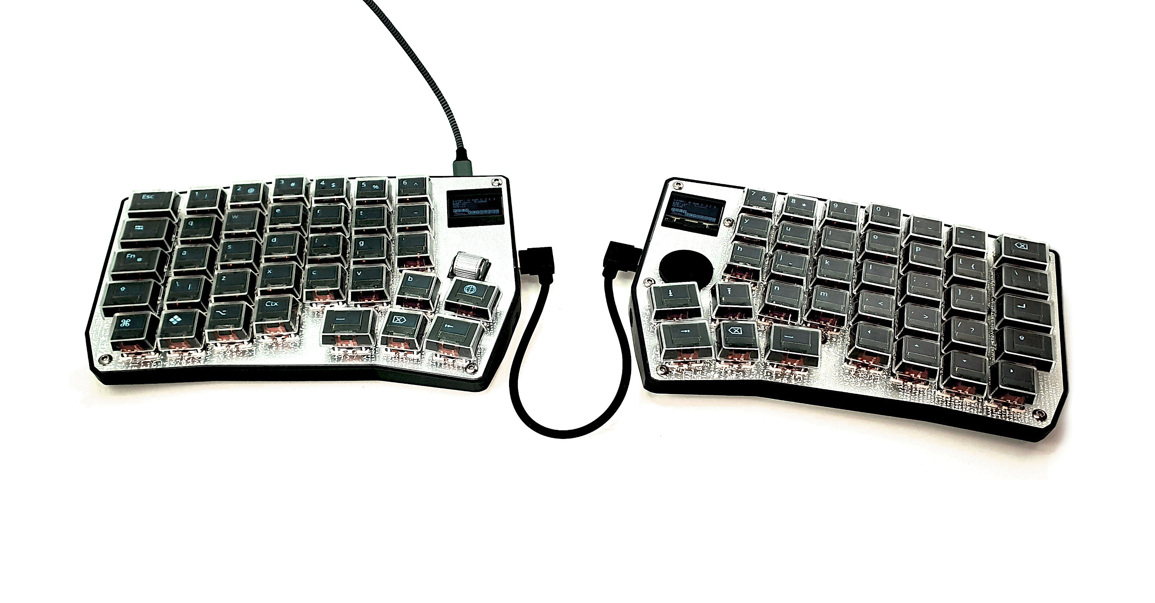
images/PolyKybdSplit72.jpg
