thpoll83/PolyKybd/images/PolyKybdSplit72_high_res.jpg

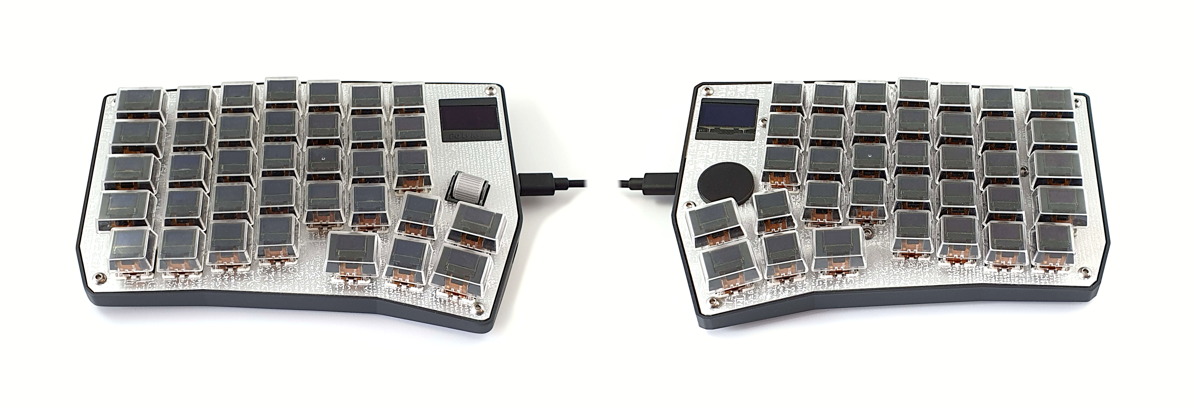
images/PolyKybdSplit72_high_res.jpg
