thpoll83/PolyKybd/images/PolyKybdSplit72p.jpg

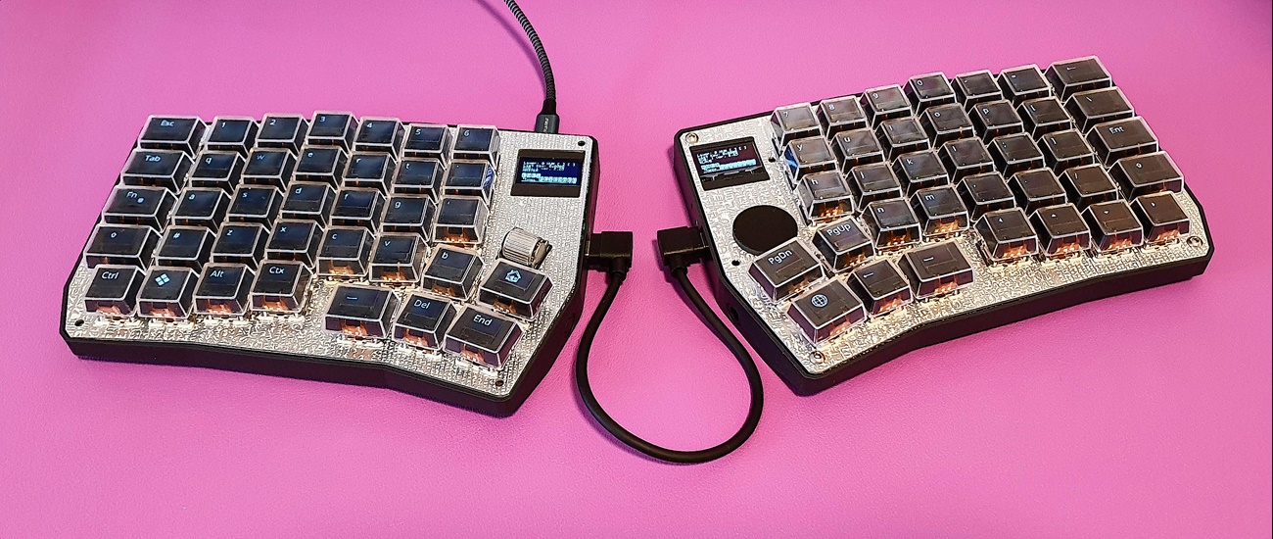
images/PolyKybdSplit72p.jpg
