thpoll83/PolyKybd/images/split42_left_gerber_4layers.png

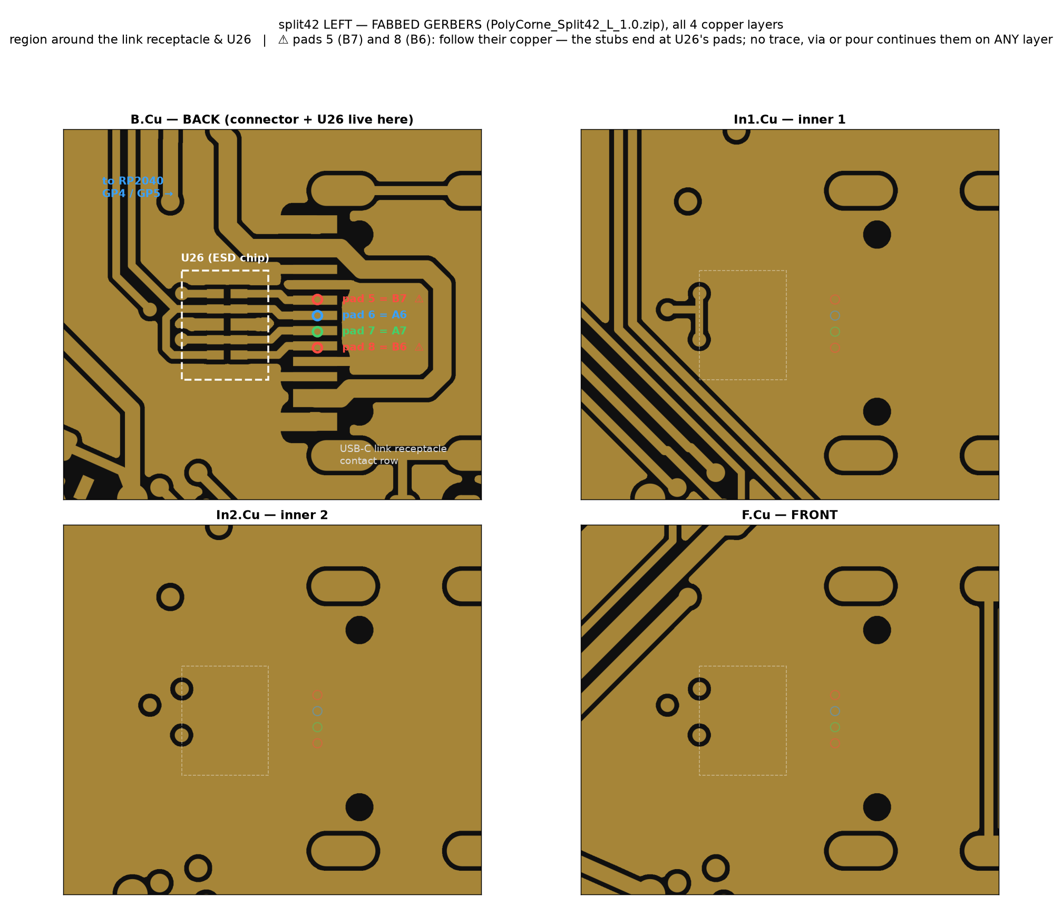
images/split42_left_gerber_4layers.png
