thpoll83/PolyKybd/images/split42_link_copper_comparison.png

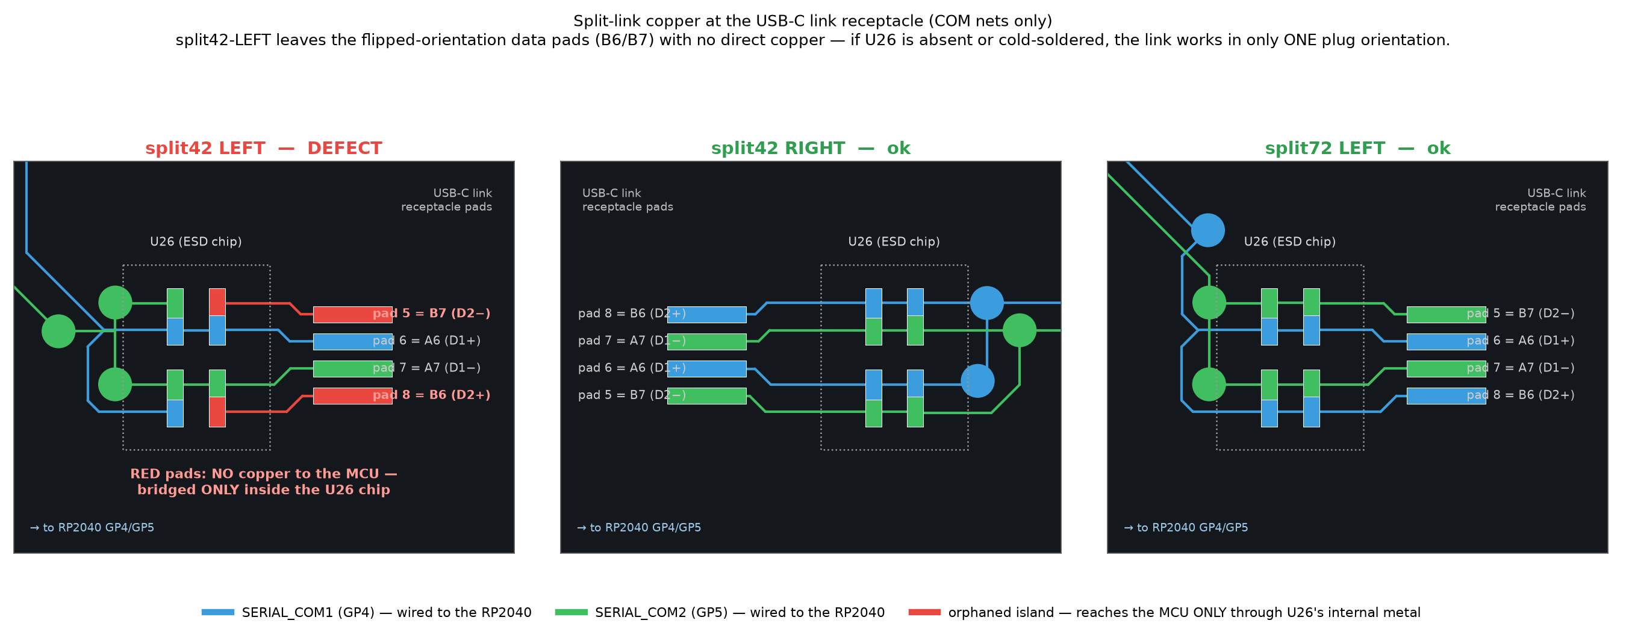
images/split42_link_copper_comparison.png
