thpoll83/PolyKybd/polykybd.png

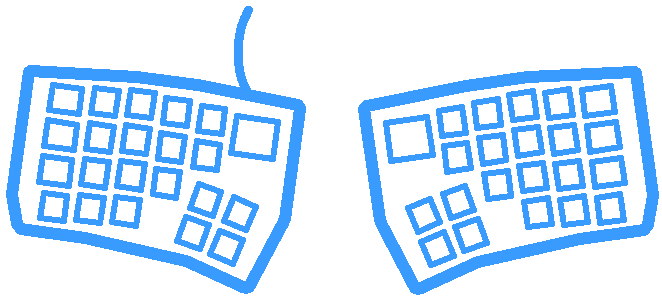
polykybd.png
