thpoll83/PolyKybd/render/textures/braid.png

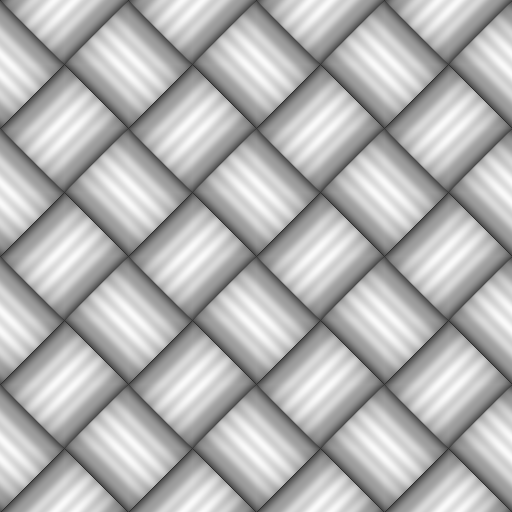
render/textures/braid.png
