thpoll83/PolyKybd/render/textures/display_front.png

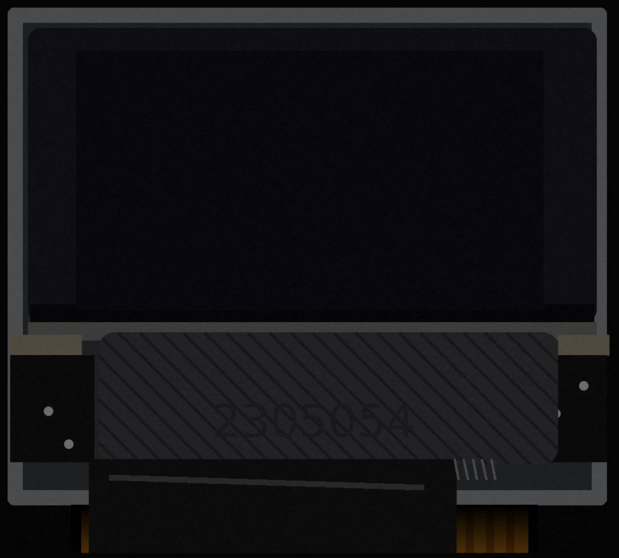
render/textures/display_front.png
