thpoll83/PolyKybd/render/textures/display_front_top.png

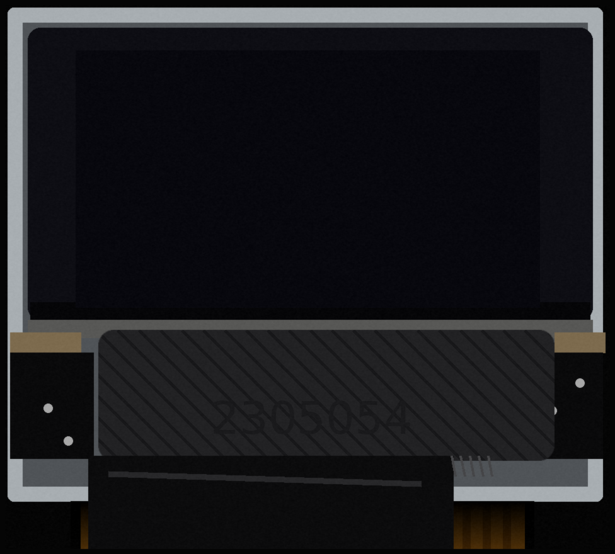
render/textures/display_front_top.png
