thpoll83/PolyKybd/render/textures/display_rim.png

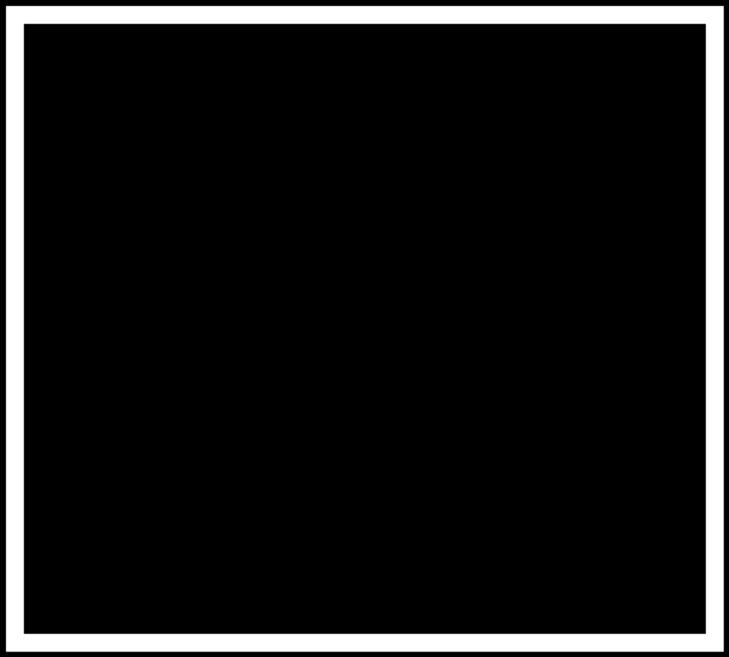
render/textures/display_rim.png
