thpoll83/PolyKybd/render/textures/flex.png

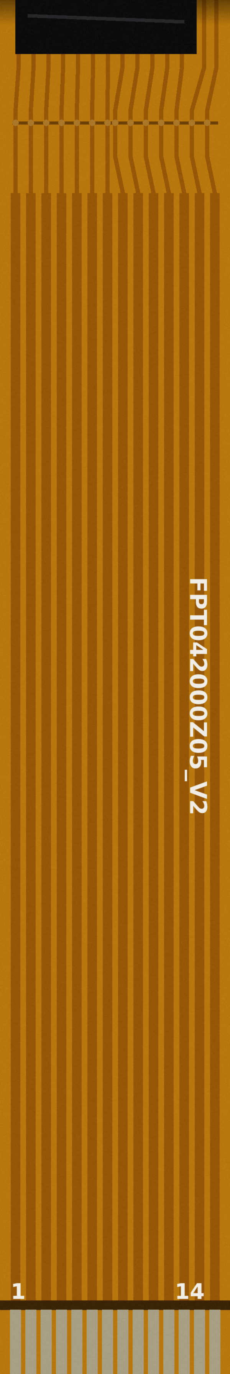
render/textures/flex.png
