thpoll83/PolyKybd/render/textures/flex_traces.png

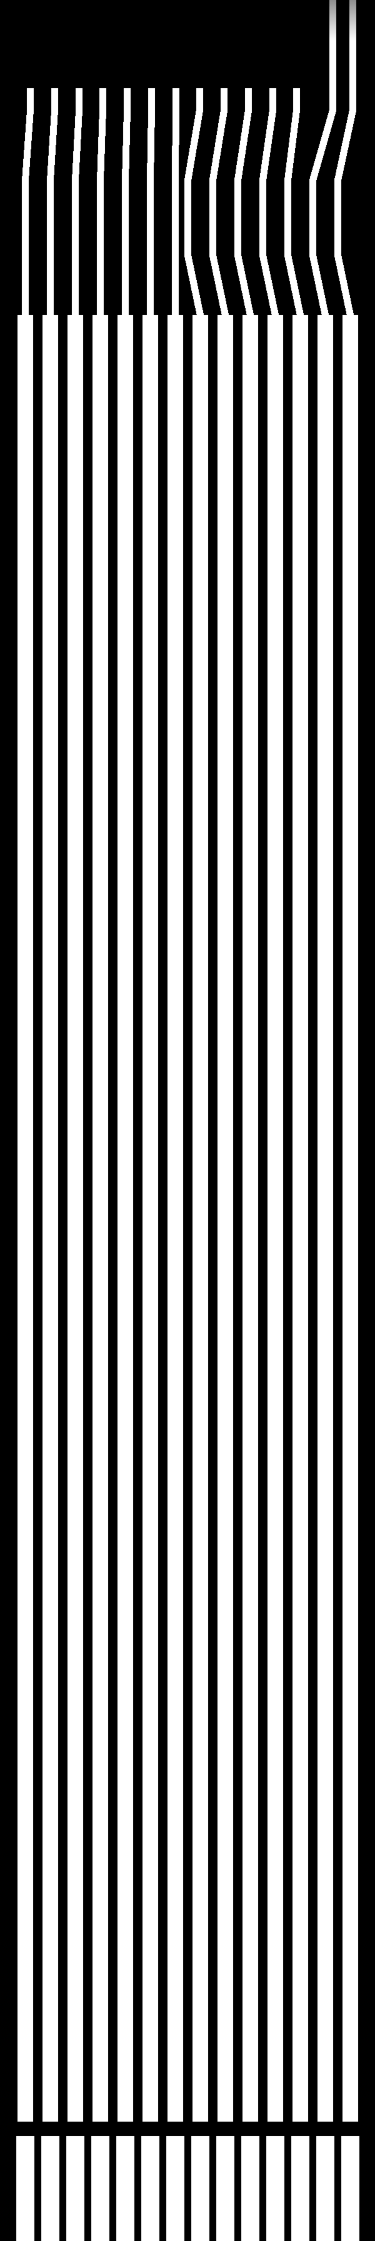
render/textures/flex_traces.png
