thpoll83/PolyKybd/render/textures/screens_gimp_l1.png

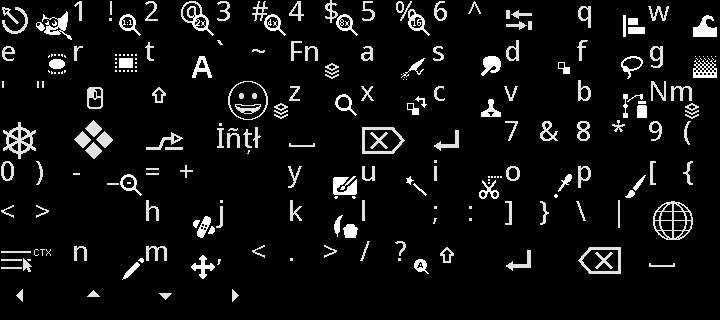
render/textures/screens_gimp_l1.png
