thpoll83/PolyKybd/render/textures/screens_layer0.png

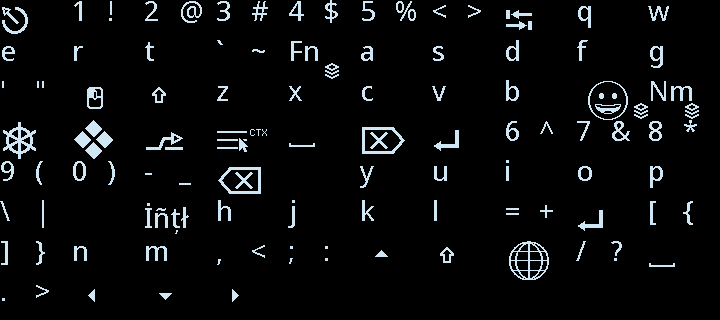
render/textures/screens_layer0.png
