thpoll83/PolyKybd/render/textures/screens_layer1.png

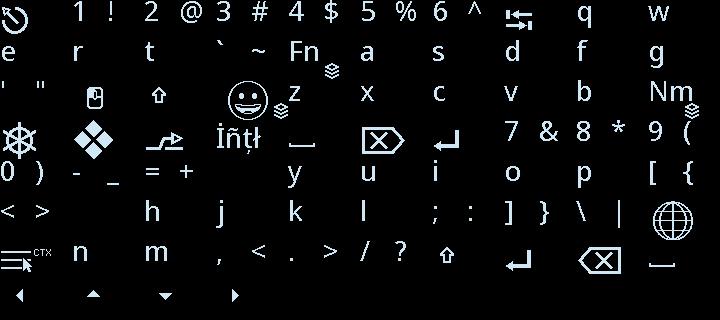
render/textures/screens_layer1.png
