thpoll83/PolyKybd/render/textures/source/oled_module_photo.jpg

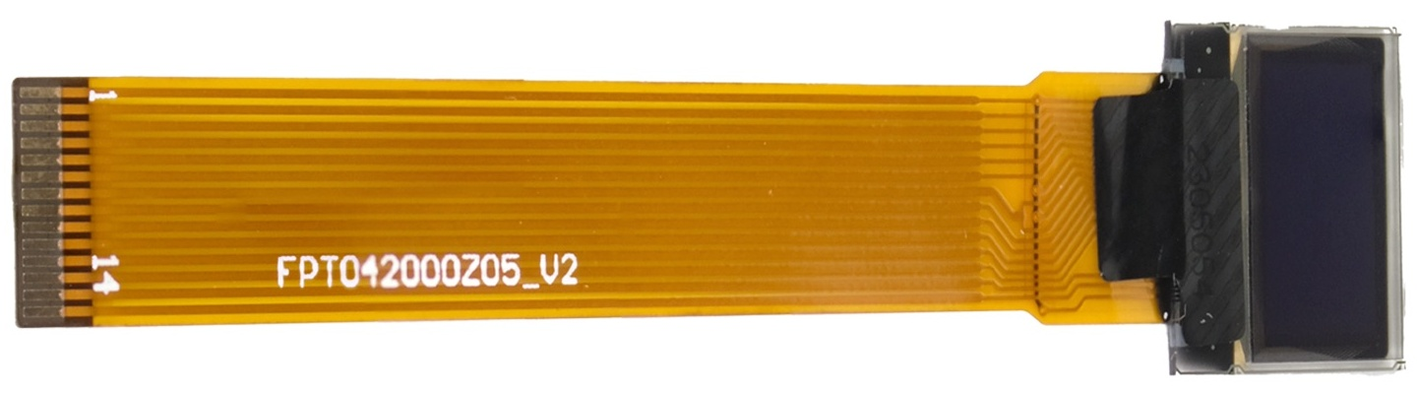
render/textures/source/oled_module_photo.jpg
