thpoll83/PolyKybd/RoHS/PolyKybd-RoHS-Compliance-Matrix.xlsx

Sheet: Compliance Matrix
PolyKybd - RoHS Compliance Matrix
CE Technical File appendix - Directive 2011/65/EU (RoHS) as amended by (EU) 2015/863. All references verified against files in repository /RoHS. Prepared 2026-07-12.
Ref / Designators | Component / Value | Qty | Manufacturer | RoHS Evidence Document | Evidence Type | Applicable Standard | Status | Notes / Action
ELECTRICAL COMPONENTS (populated BOM)
C1_1-C1_36 | 2.2uF 0603 25V | 36 | Samsung | 2304140030_Samsung-Electro-Mechanics-CL05A105KA5NQNC_C52923.pdf | Manufacturer material/RoHS report (Samsung MLCC) | RoHS 2011/65/EU as amended by (EU) 2015/863 | Documented
C2,C3_1-C3_36,C5_1-C5_36,C6_1-C6_36,C24,C25,C30-C32 | 1uF 0402 16V | 114 | Samsung | 2304140030_Samsung-Electro-Mechanics-CL05A105KA5NQNC_C52923.pdf | Manufacturer material/RoHS report (Samsung MLCC) | RoHS 2011/65/EU as amended by (EU) 2015/863 | Documented
C2_1-C2_36 | 2.2uF 0603 16V | 36 | Samsung | 2304140030_Samsung-Electro-Mechanics-CL05A105KA5NQNC_C52923.pdf | Manufacturer material/RoHS report (Samsung MLCC) | RoHS 2011/65/EU as amended by (EU) 2015/863 | Documented
C3,C8 | 27pF 0402 16V | 2 | Samsung | 2304140030_Samsung-Electro-Mechanics-CL05A105KA5NQNC_C52923.pdf | Manufacturer material/RoHS report (Samsung MLCC) | RoHS 2011/65/EU as amended by (EU) 2015/863 | Documented
C4,C10 | 4.7uF 0805 25V | 2 | Samsung | 2304140030_Samsung-Electro-Mechanics-CL05A105KA5NQNC_C52923.pdf | Manufacturer material/RoHS report (Samsung MLCC) | RoHS 2011/65/EU as amended by (EU) 2015/863 | Documented
C4_1-C4_36,C33,C34 | 4.7uF 3216 25V Tantalum (293D475X9025A2TE3) | 38 | Vishay | vishay-rohs-20250901.pdf | Manufacturer RoHS Compliance Statement, 1 Sep 2025, signed COO | RoHS 2002/95/EG, 2011/65/EU, 2015/863/EU (RoHS I-III) | Documented | Replaced EOL Sunlord C118249 with Vishay C5380411 (v3.3). The E3 termination suffix is Vishay's lead-free code; the 293D datasheet specifies 100% matte tin terminations.
C5,C11 | 6.8pF 0603 50V | 2 | Samsung | 2304140030_Samsung-Electro-Mechanics-CL05A105KA5NQNC_C52923.pdf | Manufacturer material/RoHS report (Samsung MLCC) | RoHS 2011/65/EU as amended by (EU) 2015/863 | Documented | Blanket 'all our MLCCs' declaration (p.2). The v3.3 part CL10C6R8CB8NNNC (C318672) is not named anywhere in the document, and the superseded CL10C6R8DB8NNNC appears on p.14 which the current appendix page selection (1,2,13,19,25) does not include. Same category as Silergy: linkage via the reference table and section divider. Consider adding p.14.
C6,C12-C14,C26 | 10uF 0805 16V | 5 | Samsung | 2304140030_Samsung-Electro-Mechanics-CL05A105KA5NQNC_C52923.pdf | Manufacturer material/RoHS report (Samsung MLCC) | RoHS 2011/65/EU as amended by (EU) 2015/863 | Documented
C9,C15-C23 | 100nF 0402 16V | 10 | Samsung | 2304140030_Samsung-Electro-Mechanics-CL05A105KA5NQNC_C52923.pdf | Manufacturer material/RoHS report (Samsung MLCC) | RoHS 2011/65/EU as amended by (EU) 2015/863 | Documented
D1 | Red 0805 C84256 | 1 | NationStar | 2409272203_Foshan-NationStar-Optoelectronics-NCD0805R1_C84256.pdf | Manufacturer specification (NationStar LED) | RoHS 2011/65/EU as amended by (EU) 2015/863 | Documented
D1_1-D1_36,D12 | 1N4148WSX | 37 | Shenzhen JingYang | 2405091035_Shenzhen-JingYang-1N4148WSX_C6423741.pdf | Manufacturer datasheet (Pb-free / lead-free stated) | RoHS 2011/65/EU as amended by (EU) 2015/863 | Documented
D2 | 1N5819WS | 1 | Hottech | ROHS3HOTTECH.pdf | Third-party test report (BST, RoHS 2) - diode package family | RoHS 2011/65/EU as amended by (EU) 2015/863 | Documented | 1N5819WS (SOD-323). Hottech/BST RoHS 2 test report includes 323-series package testing, and the assembly house (JLCPCB) additionally marks the part RoHS-compliant. Accepted.
D5 | Green 0805 C2297 | 1 | Hubei KENTO | C2297.pdf | Manufacturer specification (KENTO 0805 green LED, RoHS stated) | RoHS 2011/65/EU as amended by (EU) 2015/863 | Documented
D6 | Yellow 0805 C2296 | 1 | Hubei KENTO | 1806151129_Hubei-KENTO-Elec-KT-0805Y_C2296.pdf | Manufacturer specification (KENTO LED) | RoHS 2011/65/EU as amended by (EU) 2015/863 | Documented
FB1,FB2 | GZ2012D601TF | 2 | Sunlord | 2310301640_Sunlord-GZ2012D601TF_C1017.pdf | Manufacturer part-specific RoHS document (Sunlord GZ2012D601TF) | RoHS 2011/65/EU as amended by (EU) 2015/863 | Documented | Part-specific Sunlord RoHS document for GZ2012D601TF.
J1-J36 | FH34SRJ-14S-0.5SH | 36 | JUSHUO | FH34SRJ-14S-0.5SH(50)_CL0580-1252-8-50_SpecSheet_0000414509.pdf | Manufacturer spec sheet (states 'This product is RoHS compliant') | RoHS 2011/65/EU as amended by (EU) 2015/863 | Documented
J37 | FH34SRJ-12S-0.5SH | 1 | Hirose | FH34SRJ-12S-0.5SH(99)_CL0580-1253-0-99_SpecSheet_0000414526.pdf | Manufacturer spec sheet (states 'This product is RoHS compliant') | RoHS 2011/65/EU as amended by (EU) 2015/863 | Documented
J39 | FH12-30S-0.5SH | 1 | Hirose | FH12-30S-05SH.pdf | Distributor listing (RoHS (EU)2015/863 stated) | RoHS 2011/65/EU as amended by (EU) 2015/863 | Documented
L1,L2 | 2.2uH | 2 | SXN | 2108131530_SXN-Shun-Xiang-Nuo-Elec-SMMS0420-2R2M_C133191.pdf | Manufacturer datasheet (SXN inductor) | RoHS 2011/65/EU as amended by (EU) 2015/863 | Documented
LED1-LED36 | XL-3030RGBC | 36 | Xinglight | 2402181502_XINGLIGHT-XL-3030RGBC-WS2812B_C5349958.pdf | Manufacturer technical data sheet (Xinglight LED) | RoHS 2011/65/EU as amended by (EU) 2015/863 | Documented
R1,R2 | 22 0603 | 2 | Yageo | 2304140030_YAGEO-RC0603JR-0710ML_C141675.pdf | Manufacturer datasheet (RoHS compliant & halogen-free stated) | RoHS 2011/65/EU as amended by (EU) 2015/863 | Documented
R1_1-R1_36,R15,R20,R25 | 10k 0402 | 39 | Yageo | 2304140030_YAGEO-RC0603JR-0710ML_C141675.pdf | Manufacturer datasheet (RoHS compliant & halogen-free stated) | RoHS 2011/65/EU as amended by (EU) 2015/863 | Documented
R3,R4,R7,R9 | 5.1K 0402 | 4 | Yageo | 2304140030_YAGEO-RC0603JR-0710ML_C141675.pdf | Manufacturer datasheet (RoHS compliant & halogen-free stated) | RoHS 2011/65/EU as amended by (EU) 2015/863 | Documented
R5,R6,R16,R19,R21 | 1k 0402 | 5 | Yageo | 2304140030_YAGEO-RC0603JR-0710ML_C141675.pdf | Manufacturer datasheet (RoHS compliant & halogen-free stated) | RoHS 2011/65/EU as amended by (EU) 2015/863 | Documented
R8 | 5.6K 0402 | 1 | Yageo | 2304140030_YAGEO-RC0603JR-0710ML_C141675.pdf | Manufacturer datasheet (RoHS compliant & halogen-free stated) | RoHS 2011/65/EU as amended by (EU) 2015/863 | Documented
R10,R11,R30 | 390k 0603 1% | 3 | Yageo | 2304140030_YAGEO-RC0603JR-0710ML_C141675.pdf | Manufacturer datasheet (RoHS compliant & halogen-free stated) | RoHS 2011/65/EU as amended by (EU) 2015/863 | Documented
R12,R17 | 150k 0603 | 2 | Yageo | 2304140030_YAGEO-RC0603JR-0710ML_C141675.pdf | Manufacturer datasheet (RoHS compliant & halogen-free stated) | RoHS 2011/65/EU as amended by (EU) 2015/863 | Documented
R13 | 12k 0603 | 1 | Yageo | 2304140030_YAGEO-RC0603JR-0710ML_C141675.pdf | Manufacturer datasheet (RoHS compliant & halogen-free stated) | RoHS 2011/65/EU as amended by (EU) 2015/863 | Documented
R14 | 680k 0603 | 1 | Yageo | 2304140030_YAGEO-RC0603JR-0710ML_C141675.pdf | Manufacturer datasheet (RoHS compliant & halogen-free stated) | RoHS 2011/65/EU as amended by (EU) 2015/863 | Documented
R18 | 10M 0603 | 1 | Yageo | 2304140030_YAGEO-RC0603JR-0710ML_C141675.pdf | Manufacturer datasheet (RoHS compliant & halogen-free stated) | RoHS 2011/65/EU as amended by (EU) 2015/863 | Documented
R22,R23 | 27 0603 | 2 | Yageo | 2304140030_YAGEO-RC0603JR-0710ML_C141675.pdf | Manufacturer datasheet (RoHS compliant & halogen-free stated) | RoHS 2011/65/EU as amended by (EU) 2015/863 | Documented
R24 | 2M2 0603 | 1 | Yageo | 2304140030_YAGEO-RC0603JR-0710ML_C141675.pdf | Manufacturer datasheet (RoHS compliant & halogen-free stated) | RoHS 2011/65/EU as amended by (EU) 2015/863 | Documented
SW2,SW3 | EVQPUC02K | 2 | Panasonic | panasonic_rohs_2ma_2000379.pdf | Manufacturer non-use report for chemical substances (RoHS) | RoHS 2011/65/EU as amended by (EU) 2015/863 | Documented
SW_K_1-SW_K_36 | Kailh CPG151101S11-16 | 36 | Kailh | 2208291600_Kailh-CPG151101S11-16_C5156480.pdf | Manufacturer drawing ('ABIDE BY ROHS') | RoHS 2011/65/EU as amended by (EU) 2015/863 | Documented
U1,U2 | TLV62569DBVR | 2 | TI | TexasTLV62569DBVR.pdf | Manufacturer package addendum (Green / RoHS, no Sb/Br) | RoHS 2011/65/EU as amended by (EU) 2015/863 | Documented
U3 | SY6280AAC | 1 | Silergy | ROHS-2024-SilergyCorp.pdf | Third-party RoHS test report (SGS, Jan 2024) | RoHS 2011/65/EU as amended by (EU) 2015/863 | Documented
U4-U8 | 74HC595BQ | 5 | Nexperia | Nexperia - Statement on RoHS 20241008.pdf | Manufacturer RoHS statement | RoHS 2011/65/EU as amended by (EU) 2015/863 | Documented | Statement is company-wide across all Nexperia semiconductor products. Its exemption appendix (p.3) lists 37 packages relying on RoHS exemptions 7(a)/7(c)-I; DHVQFN-16 is NOT among them, so this part is compliant outright. Part recoded C3303719 -> C730243 in v3.3 (same MPN, 74HC595BQ,115).
U9 | W25Q64JVXGIM | 1 | Winbond | winbond-W25Q64JV-rohs.png | Manufacturer RoHS statement (image scan) | RoHS 2002/95/EU (as cited by the evidence) | Documented - directive version outdated | ACTION: the evidence is p.59 of the W25Q64JV datasheet and its RoHS note cites 2002/95/EU, which is superseded by 2011/65/EU + (EU) 2015/863. Request a current declaration from Winbond. Coverage of the part itself is fine: the document is titled W25Q64JV (the family), so it covers XGIM exactly as it covered XGIQ. Part changed C2940195 -> C5440778 in v3.3.
U10 | RP2040 | 1 | Raspberry Pi | rp2040-rohs.png | Manufacturer RoHS statement (image scan) | RoHS 2011/65/EU as amended by (EU) 2015/863 | Documented
U11,U26 | TPD4E05U06DQAR | 2 | MSKSEMI | C2836386-TPD4E05U06DQAR-MS.pdf | Manufacturer material statement (MSKSEMI) | RoHS 2011/65/EU as amended by (EU) 2015/863 | Documented
U12-U25 | 74AHC1G125GW,125 | 14 | Nexperia | Nexperia - Statement on RoHS 20241008.pdf | Manufacturer RoHS statement | RoHS 2011/65/EU as amended by (EU) 2015/863 | Documented | Retargeted from the EOL TI C151890 to Nexperia C85397 in v3.3, so the TI datasheet no longer applies and sn74lvc1g126.pdf was deleted. Covered by the company-wide Nexperia statement; SOT-353 is NOT in its lead-exemption appendix, so compliant outright. One buffer per package: qty 14 = U12-U25, and the old 'U?,U?' placeholders are resolved.
USB1,USB2 | TYPE-C-31-M-12 | 2 | Hroparts | 2410010003_Korean-Hroparts-Elec-TYPE-C-31-M-12_C165948.pdf | Manufacturer drawing ('ROHS') | RoHS 2011/65/EU as amended by (EU) 2015/863 | Documented
Y1 | 7M12000044 | 1 | TXC | TXC-7M12000044.pdf | Manufacturer specification (TXC crystal) | RoHS 2011/65/EU as amended by (EU) 2015/863 | Documented
BARE PCB (substrate, incl. exposed copper of mounting holes & test points)
PCB (all) | Printed circuit board - ENIG & Lead-free HASL finish | - | JLCPCB (Shenzhen JLC) | rohs-certificate-of-conformity.pdf | Declaration of Conformity (Soar Testing, 2025-12-01; EN 62321 methods; covers HASL + ENIG) | RoHS 2011/65/EU as amended by (EU) 2015/863 | Documented | Also on file: RoHS Certificate of Conformity- ENIG_JLCPCB.pdf (2023) and ROHS2.0 Test Report - ENIG_JLCPCB_.pdf. Covers bare-board copper of mounting holes and test points.
SCOPED OUT - no separate RoHS certificate required
(pin headers) | Pin headers | - | - | n/a | Not applicable | - | Documented | Not populated (DNP) - not present in the finished product, so no substance to declare.
(mounting holes) | Mounting holes | - | - | n/a | Not applicable | - | Documented | Bare PCB copper only - covered by the PCB substrate RoHS evidence above.
(test points) | Test points | - | - | n/a | Not applicable | - | Documented | Bare PCB copper only - covered by the PCB substrate RoHS evidence above.

Sheet: Findings & Actions
Findings & Recommended Actions
# | Item | Finding / Recommended action
1 | RESOLVED - D5 (green 0805) | Re-pointed to C2297.pdf (KENTO 0805 green LED spec, RoHS stated).
2 | RESOLVED - U3 (SY6280AAC) | Re-pointed to ROHS-2024-SilergyCorp.pdf (SGS RoHS test report, Jan 2024, Silergy SMD components).
3 | RESOLVED - U12-U25 (74AHC1G125GW,125) | Part retargeted from the EOL TI SN74LVC1G126DBVR (C151890) to Nexperia 74AHC1G125GW,125 (C85397) in v3.3. Evidence re-pointed to the company-wide Nexperia RoHS statement, which cites 2011/65/EU + (EU) 2015/863; SOT-353 is not in its lead-exemption appendix. sn74lvc1g126.pdf deleted. The 'U?,U?' designator placeholders are resolved - the row now reads U12-U25, qty 14.
4 | RESOLVED - D2 (1N5819WS, SOD-323) | Accepted: the Hottech/BST report includes 323-series package testing and the assembly house marks the part RoHS-compliant.
5 | RESOLVED - Connectors | All connectors reference the Hirose spec sheet for their part, each stating 'This product is RoHS compliant' (FH12-30S for J39 states RoHS (EU)2015/863). J1-J36 = FH34SRJ-14S, J37 = FH34SRJ-12S, J39 = FH12-30S. Note: the trailing (50)/(99) in the filenames is the packaging quantity, not a spec revision, so the part-matching sheet is correct regardless of that number.
6 | RESOLVED - FB1, FB2 (GZ2012D601TF) | Generic Sunlord Declaration of Conformity is valid RoHS evidence (EU RoHS + halogen + REACH); no change needed.
7 | Note - Datasheet-type evidence | Several parts are evidenced by datasheets/spec sheets that state RoHS compliance rather than dedicated declarations (e.g. Yageo, Kailh, TI TLV62569, Hroparts, JingYang). Acceptable as manufacturer evidence; upgrade to formal DoCs only if an assessor requires.
8 | Note - Unreferenced certs on file | The /RoHS folder also contains certs not linked in the reference table (e.g. Aerosemi MT9700, Fenghua RC-02W, Prosperity MCS0530, Uniroyal 0603WAF). Confirm whether these belong to alternates/DNPs or should be linked.
9 | OPEN - U9 (W25Q64JVXGIM) | The Winbond RoHS evidence cites directive 2002/95/EU, which is superseded by 2011/65/EU as amended by (EU) 2015/863. Request a current declaration. Part coverage is not in question - the document is family-level (W25Q64JV).
10 | OPEN - C5, C11 (CL10C6R8CB8NNNC) | The v3.3 Samsung part is not named in its blanket MLCC declaration, and the superseded part is on p.14 which the appendix page selection omits. Either add p.14 and accept blanket-only coverage (consistent with how Silergy/SY6280AAC is handled) or request a part-specific declaration.
