thpoll83/PolyKybd/parts/export/diffuser/diffuser_frame_left.stl

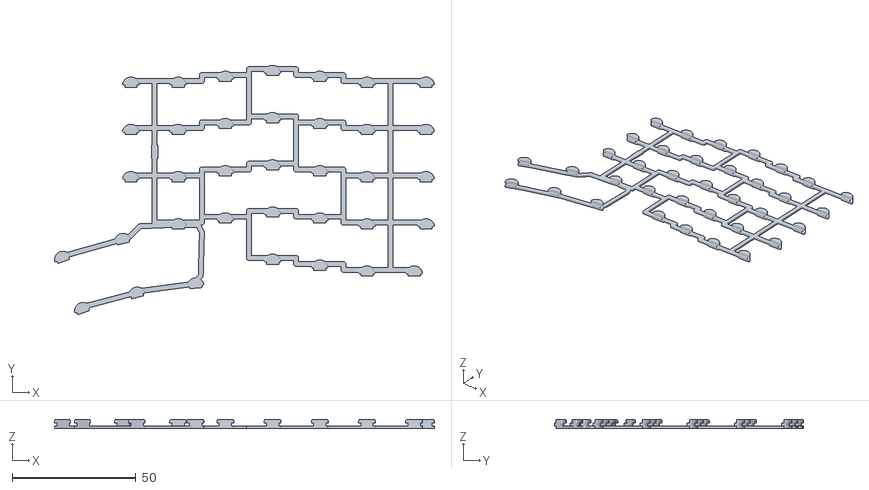
[picture p116: CAD file, 2026-08-04]
parts/export/diffuser/diffuser_frame_left.stl
153.4 x 100.7 x 3.70
