thpoll83/PolyKybd/parts/export/keycap_stem/stem_S_1U25.step

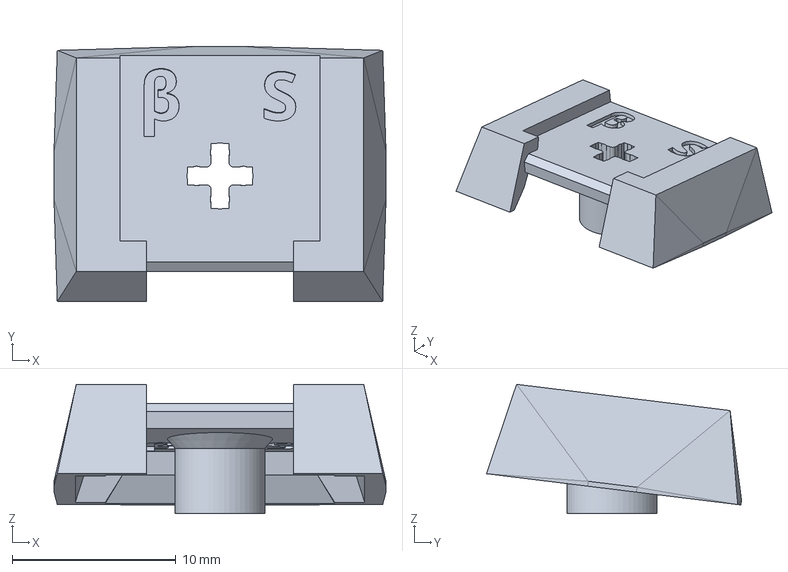
[picture p118: CAD file, 2026-10-02]
parts/export/keycap_stem/stem_S_1U25.step
20.3 x 15.6 x 7.91 mm
