thpoll83/PolyKybd/parts/export/legs/legs_v0_1p.stl

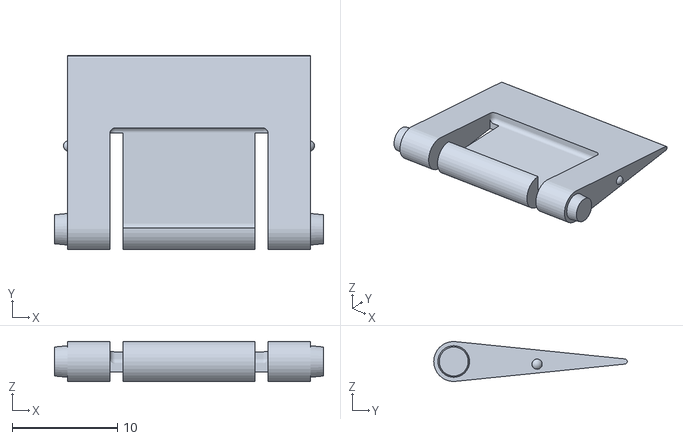
[picture p119: CAD file, 2024-03-15]
parts/export/legs/legs_v0_1p.stl
25.5 x 18.3 x 3.80
