thpoll83/PolyKybd/parts/export/rotary_enc_insert/rotary_enc_insert_r1.stl

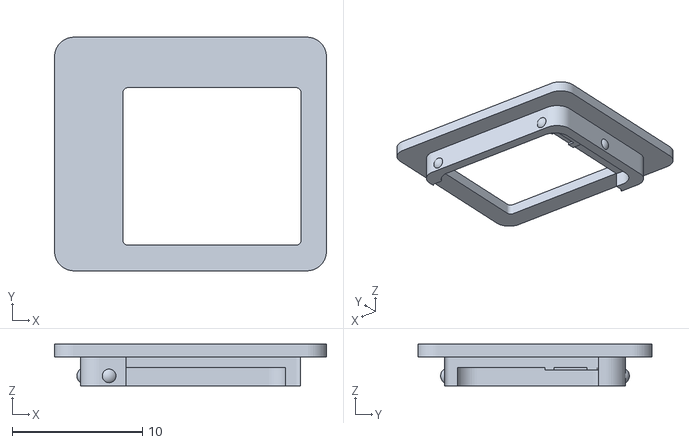
[picture p120: CAD file, 2026-08-17]
parts/export/rotary_enc_insert/rotary_enc_insert_r1.stl
20.9 x 17.9 x 3.20
