thpoll83/PolyKybd/parts/models/keycap_display.stl

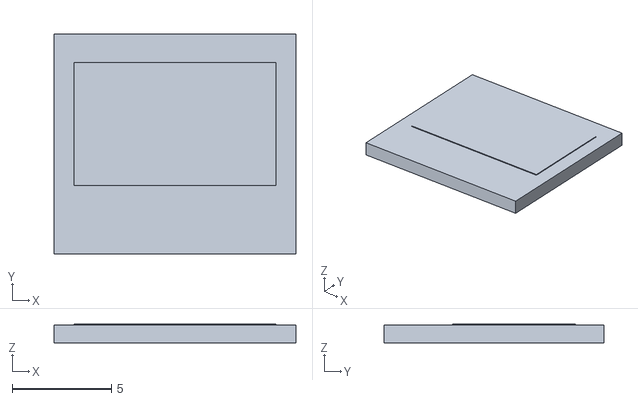
[picture p121: CAD file, 2023-03-15]
parts/models/keycap_display.stl
12.2 x 11.1 x 0.95
