thpoll83/PolyKybd/poly_kybd/models/DHVQFN-16-1EP_2.5x3.5mm_P0.5mm_EP1x2mm.step

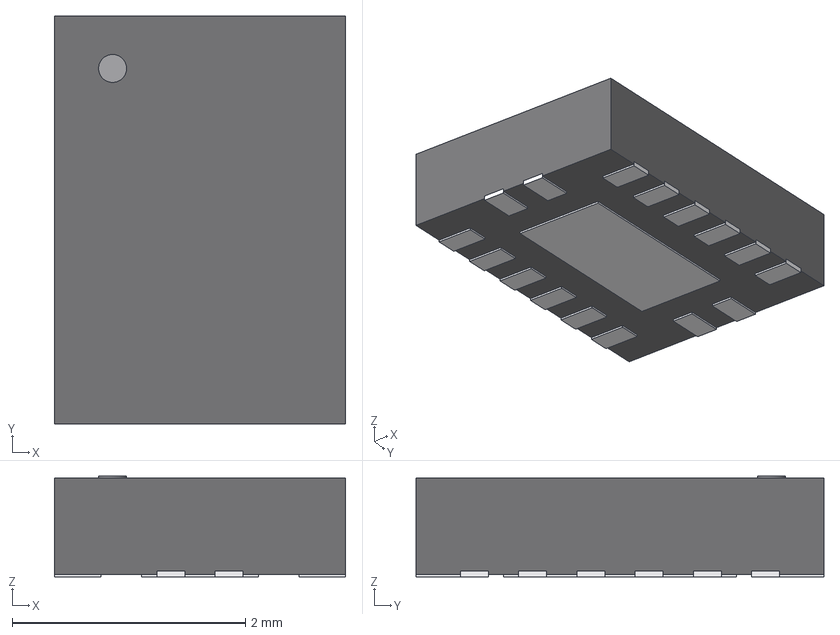
[picture p122: CAD file, 2026-10-07]
poly_kybd/models/DHVQFN-16-1EP_2.5x3.5mm_P0.5mm_EP1x2mm.step
2.50 x 3.50 x 0.865 mm
pin x 16
exposed pad
pin 1
