thpoll83/PolyKybd/poly_kybd/wave-base-left.stl

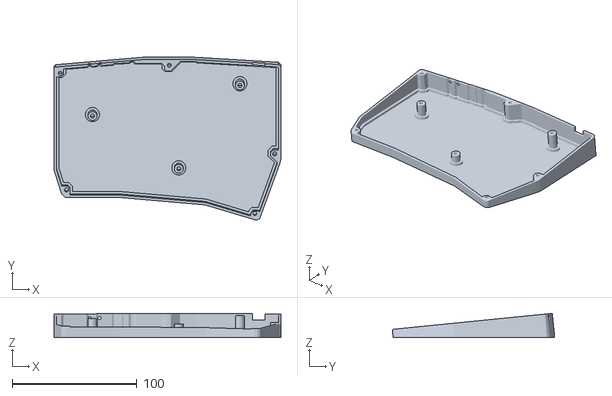
[picture p123: CAD file, 2022-05-12]
poly_kybd/wave-base-left.stl
182.1 x 130.4 x 19.5
