thpoll83/PolyKybd/parts/export/case/spacer_diffuser_frame.stl

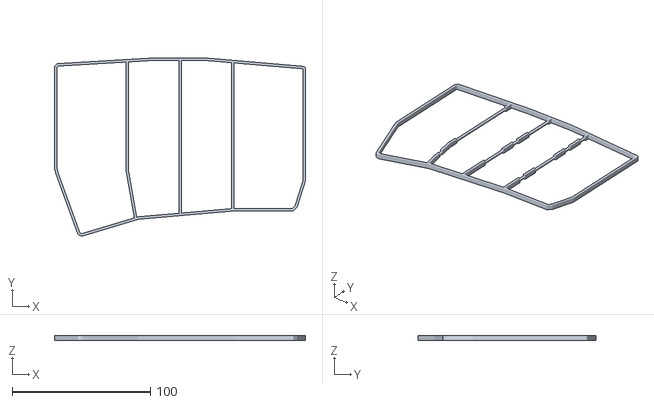
[picture p124: CAD file, 2026-08-04]
parts/export/case/spacer_diffuser_frame.stl
181.5 x 128.5 x 3.80
