thpoll83/PolyKybd/parts/export/cirque_insert/cirque23_slim_insert_r8.stl

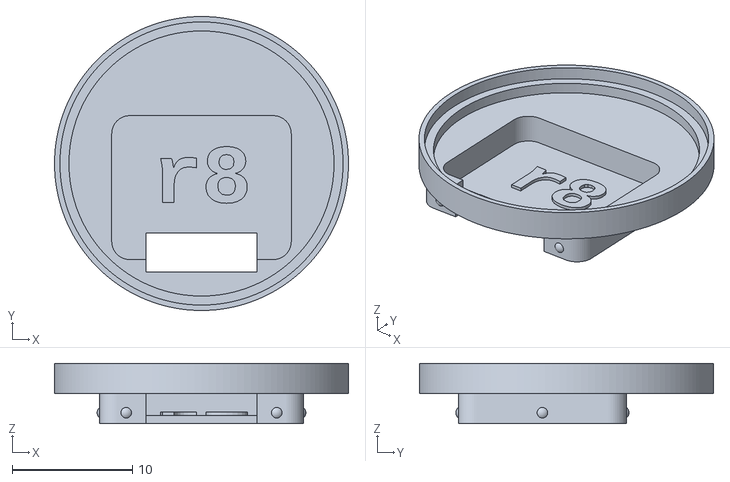
[picture p125: CAD file, 2023-09-09]
parts/export/cirque_insert/cirque23_slim_insert_r8.stl
24.4 x 24.4 x 5.01
