thpoll83/PolyKybd/parts/export/diffuser/diffuser_frame_left_4x.stl

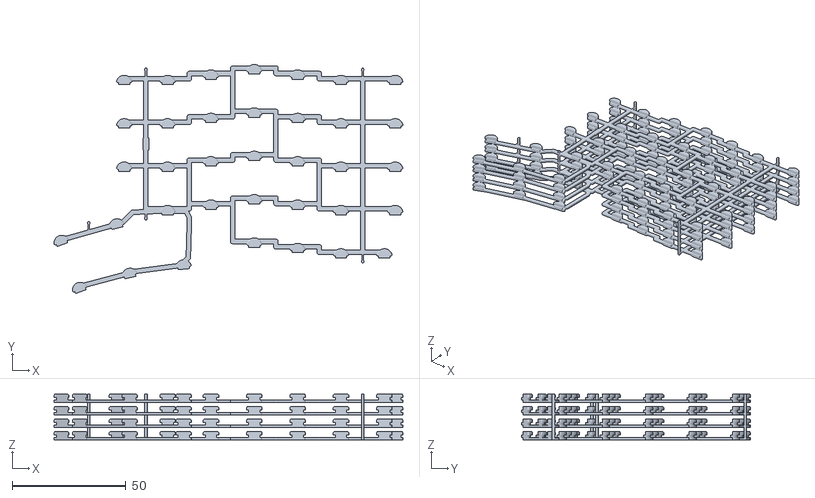
[picture p126: CAD file, 2026-08-04]
parts/export/diffuser/diffuser_frame_left_4x.stl
153.4 x 100.7 x 20.2
