thpoll83/PolyKybd/parts/export/display_holder/display_holder_r1.stl

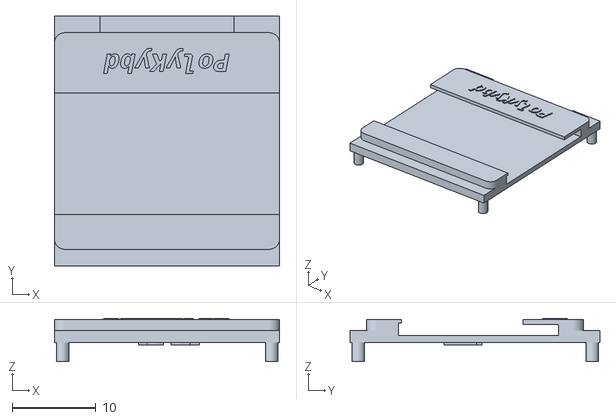
[picture p127: CAD file, 2023-09-09]
parts/export/display_holder/display_holder_r1.stl
27.0 x 29.9 x 5.15
