thpoll83/PolyKybd/parts/export/keycap_stem/keycap_stem_revAlpha_1U_R4_10p.stl

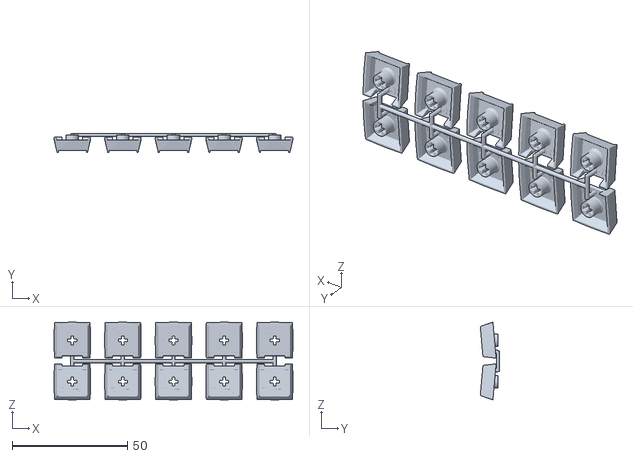
[picture p128: CAD file, 2026-08-18]
parts/export/keycap_stem/keycap_stem_revAlpha_1U_R4_10p.stl
103.9 x 8.45 x 33.7
