thpoll83/PolyKybd/parts/models/display_holder_wdisplay.stl

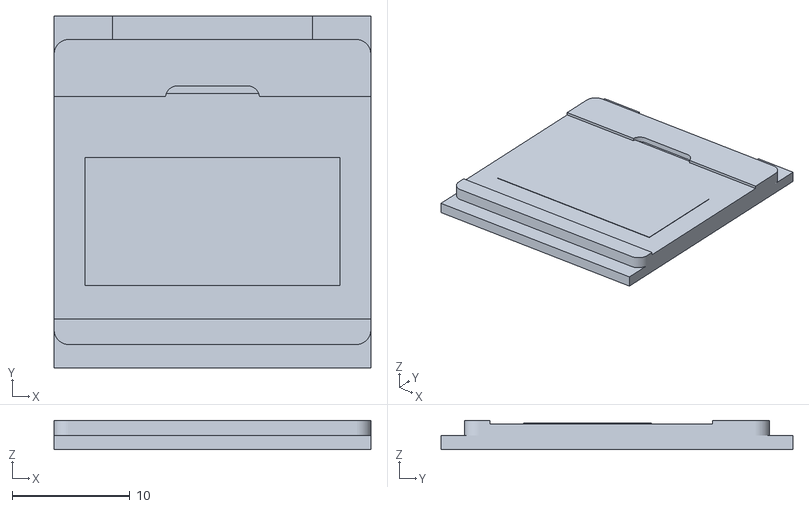
[picture p129: CAD file, 2023-03-15]
parts/models/display_holder_wdisplay.stl
27.0 x 30.0 x 2.50
