thpoll83/PolyKybd/case/case_polysplit72_right2_r5.stl

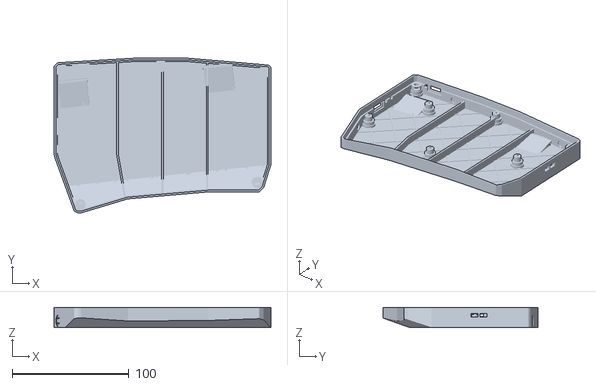
[picture p131: CAD file, 2024-07-18]
case/case_polysplit72_right2_r5.stl
185.5 x 132.5 x 17.5
