thpoll83/PolyKybd/parts/export/case/spacer_diffuser_frame_4x.stl

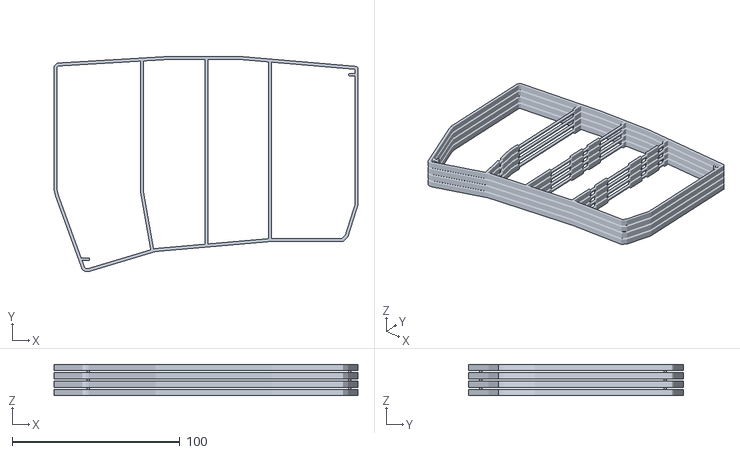
[picture p132: CAD file, 2026-08-04]
parts/export/case/spacer_diffuser_frame_4x.stl
181.5 x 128.5 x 18.8
