thpoll83/PolyKybd/parts/export/cirque_insert/cirque23_insert_high_r1.stl

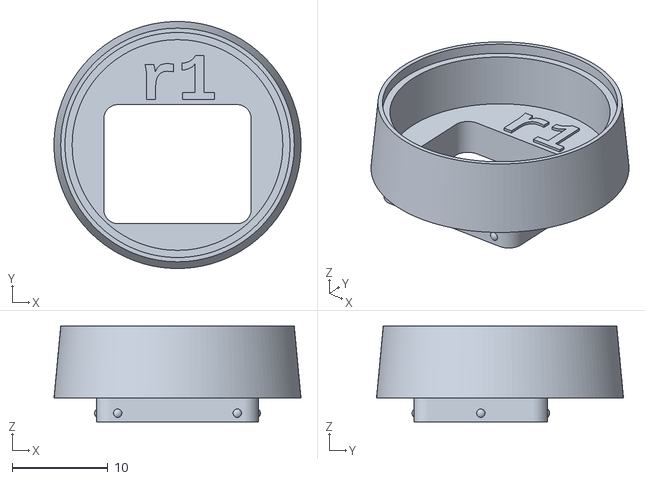
[picture p133: CAD file, 2023-09-09]
parts/export/cirque_insert/cirque23_insert_high_r1.stl
25.8 x 25.8 x 10.0
