thpoll83/PolyKybd/parts/export/keycap_stem/keycap_stem_revAlpha_1U_R3_10p.stl

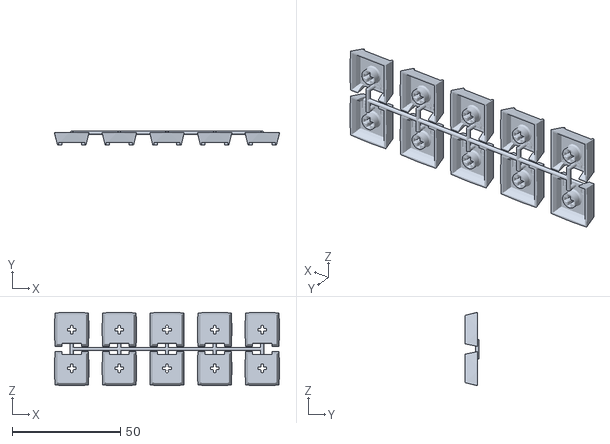
[picture p134: CAD file, 2026-08-18]
parts/export/keycap_stem/keycap_stem_revAlpha_1U_R3_10p.stl
103.9 x 6.40 x 33.8
