thpoll83/PolyKybd/parts/models/display_glass.stl

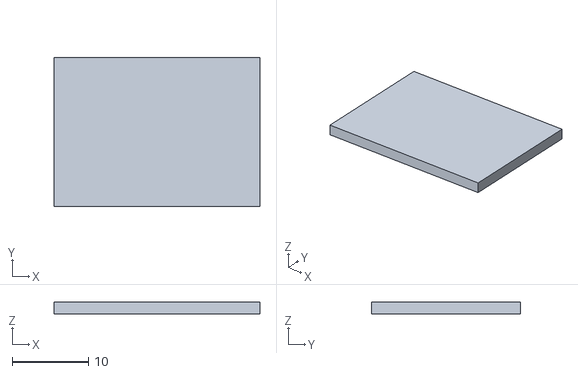
[picture p135: CAD file, 2023-03-15]
parts/models/display_glass.stl
27.0 x 19.6 x 1.60
