thpoll83/PolyKybd/poly_kybd/models/FH34SRJ-14S-0.5SH_50_.step

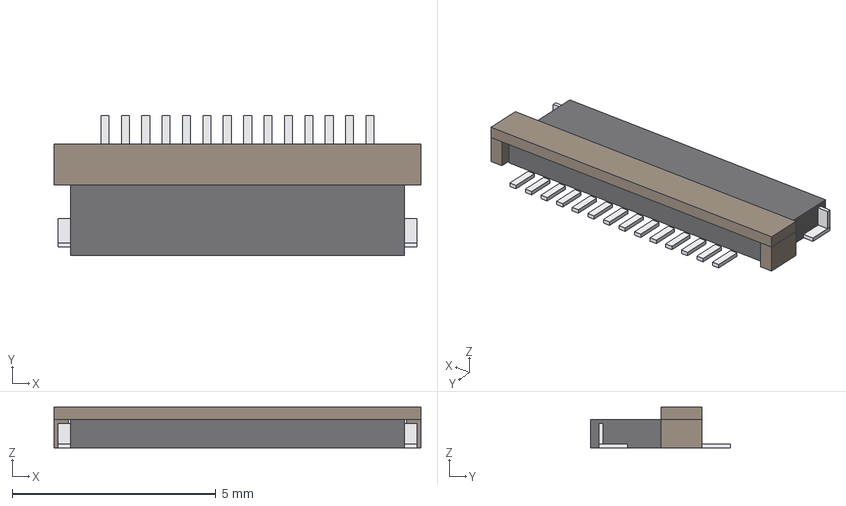
[picture p136: CAD file, 2026-10-07]
poly_kybd/models/FH34SRJ-14S-0.5SH_50_.step
9.00 x 3.42 x 1.00 mm
housing
actuator
actuator hinge x 2
lead x 14
nail x 4
