thpoll83/PolyKybd/parts/export/case/case_polykybd_split72_metal-bottom.stl

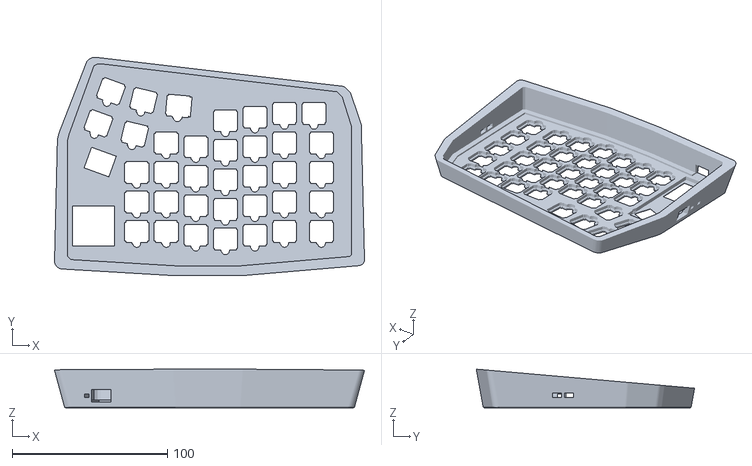
[picture p137: CAD file, 2026-06-16]
parts/export/case/case_polykybd_split72_metal-bottom.stl
200.0 x 140.7 x 25.0
