thpoll83/PolyKybd/parts/export/cirque_insert/cirque23_insert_high_r1_6p.stl

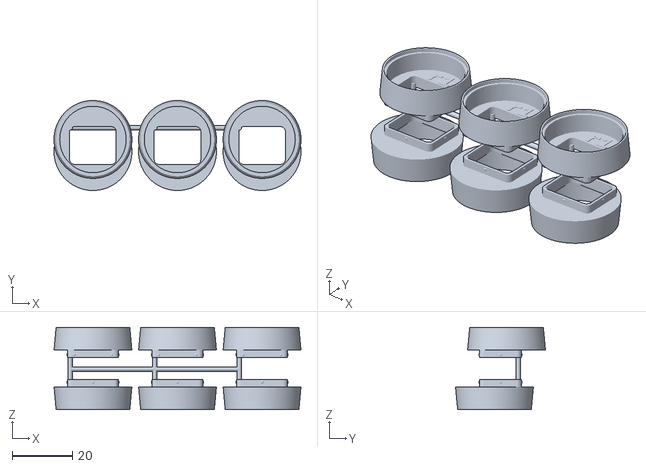
[picture p138: CAD file, 2023-06-22]
parts/export/cirque_insert/cirque23_insert_high_r1_6p.stl
81.8 x 29.8 x 27.3
