thpoll83/PolyKybd/parts/export/keycap_stem/keycap_stem_revAlpha_1U_R2_10p.stl

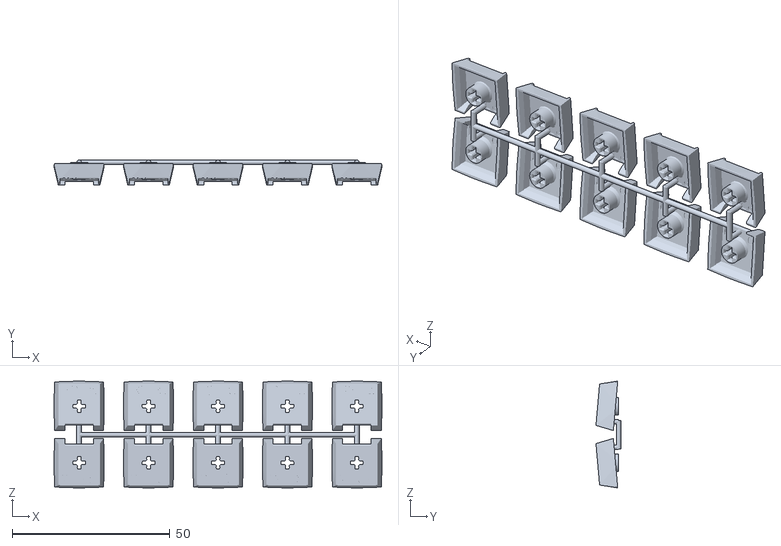
[picture p139: CAD file, 2026-08-18]
parts/export/keycap_stem/keycap_stem_revAlpha_1U_R2_10p.stl
103.9 x 7.95 x 33.8
