thpoll83/PolyKybd/case/case_polysplit72_right2_r3.stl

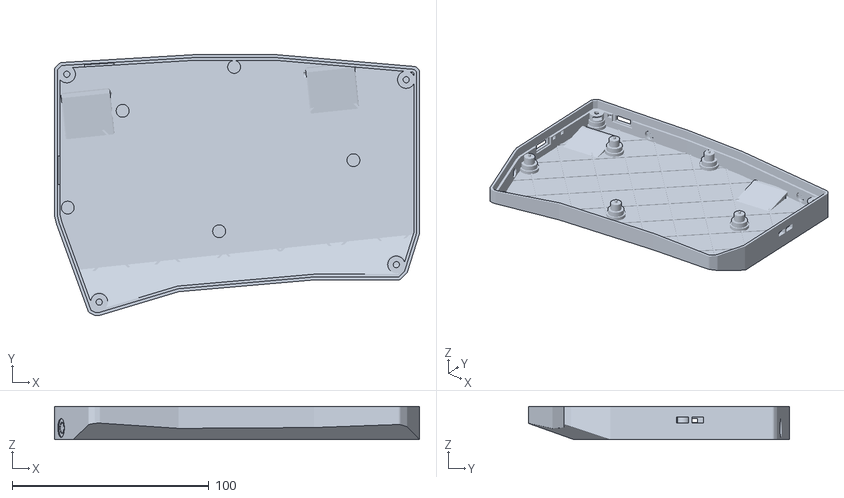
[picture p142: CAD file, 2023-12-20]
case/case_polysplit72_right2_r3.stl
185.5 x 132.5 x 17.0
