thpoll83/PolyKybd/parts/export/keycap_stem/keycap_stem_revAlpha_1U_R5_10p.stl

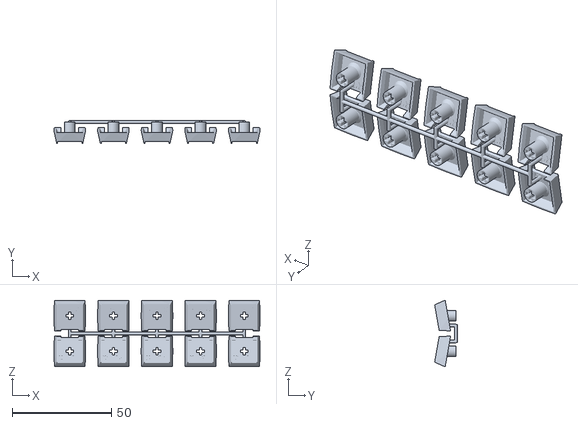
[picture p143: CAD file, 2026-08-18]
parts/export/keycap_stem/keycap_stem_revAlpha_1U_R5_10p.stl
103.9 x 11.5 x 33.5
