thpoll83/PolyKybd/parts/export/case/right_side_spacer.3mf

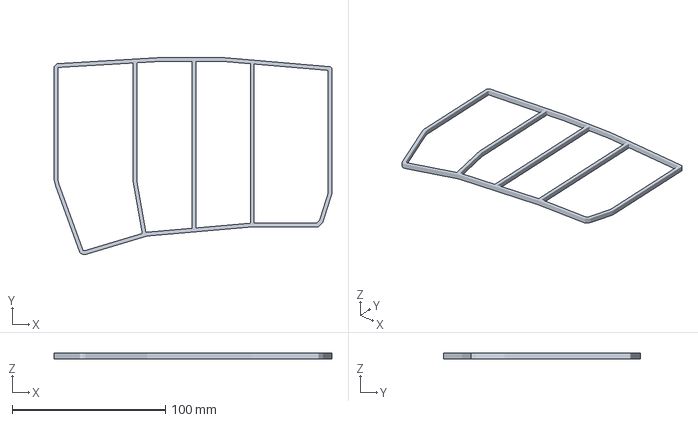
[picture p144: CAD file, 2024-07-18]
parts/export/case/right_side_spacer.3mf
181.5 x 128.5 x 3.60 mm
