thpoll83/PolyKybd/parts/export/keycap_stem/keycap_stem_revAlpha_1U25_R4_10p.stl

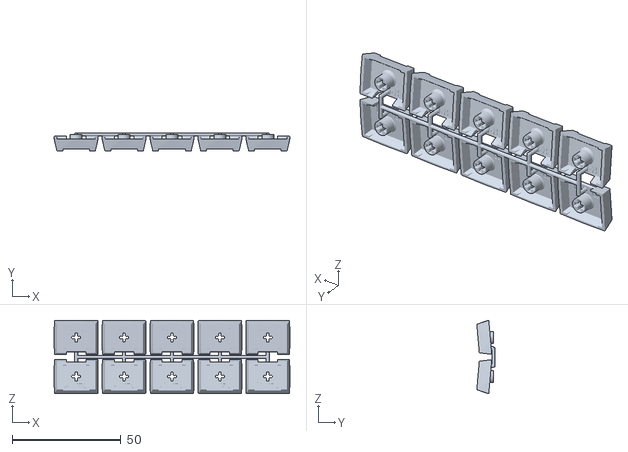
[picture p145: CAD file, 2026-08-18]
parts/export/keycap_stem/keycap_stem_revAlpha_1U25_R4_10p.stl
108.3 x 8.45 x 33.7
