thpoll83/PolyKybd/case/case_polysplit72_left2_r9.stl

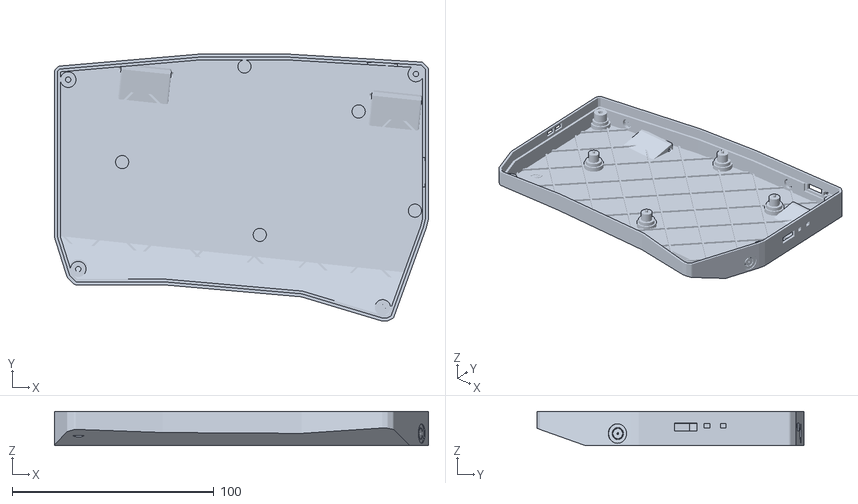
[picture p146: CAD file, 2023-09-22]
case/case_polysplit72_left2_r9.stl
185.5 x 132.5 x 17.0
