thpoll83/PolyKybd/parts/export/case/spacer_3mm8_4p.stl

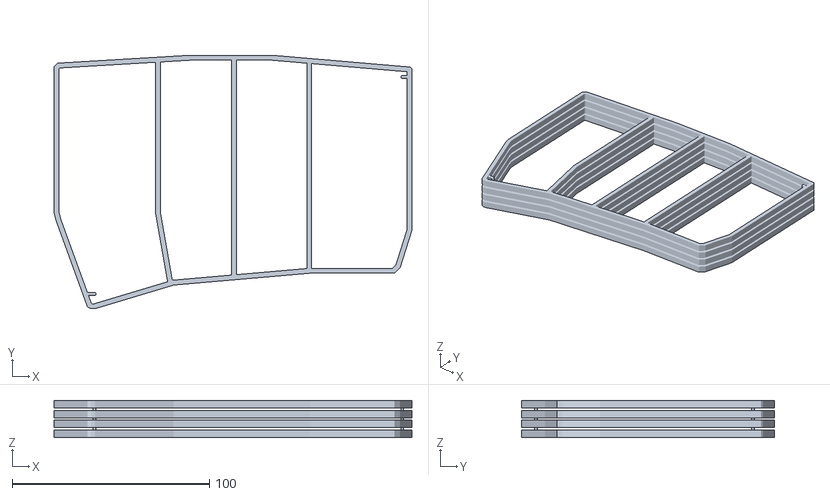
[picture p147: CAD file, 2024-03-08]
parts/export/case/spacer_3mm8_4p.stl
181.5 x 128.5 x 18.8
