thpoll83/PolyKybd/parts/export/keycap_stem/keycap_stem_revAlpha_1U25_R3_10p.stl

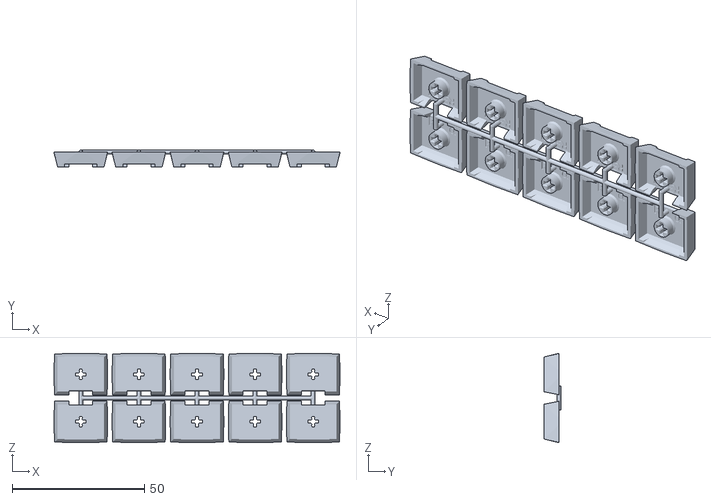
[picture p149: CAD file, 2026-08-18]
parts/export/keycap_stem/keycap_stem_revAlpha_1U25_R3_10p.stl
108.3 x 6.40 x 33.8
