thpoll83/PolyKybd/case/case_polysplit72_right2_r8_no_support.stl

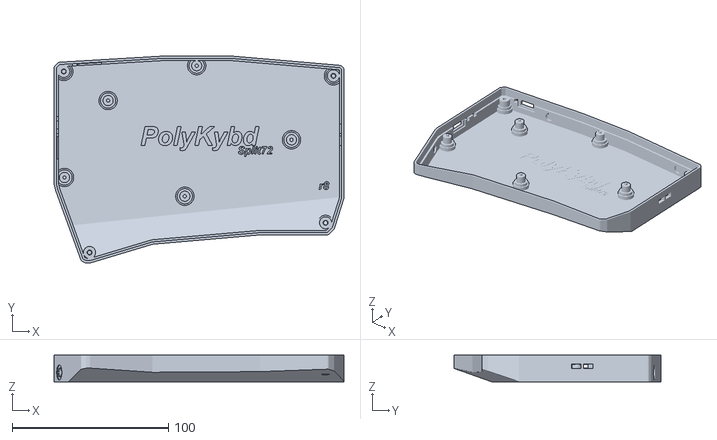
[picture p150: CAD file, 2023-09-09]
case/case_polysplit72_right2_r8_no_support.stl
185.5 x 132.5 x 17.0
