thpoll83/PolyKybd/parts/export/case/right_side_case.3mf

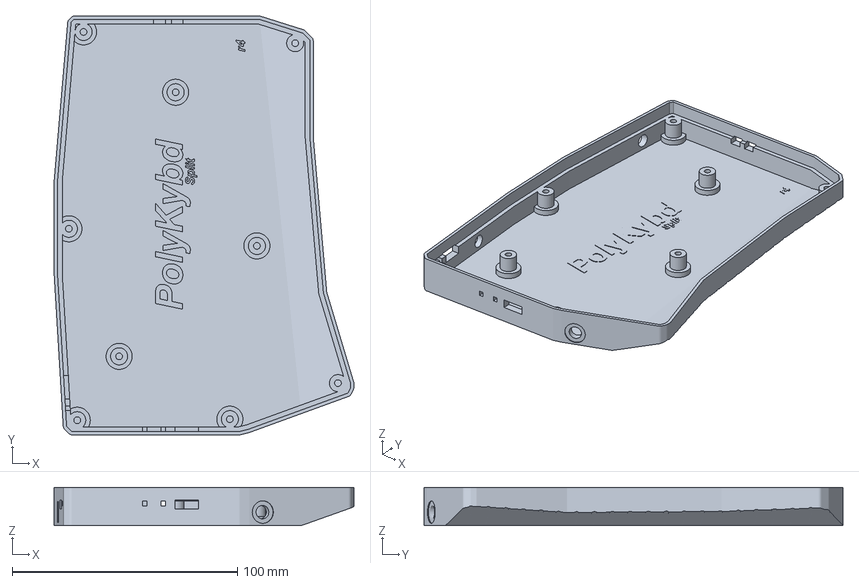
[picture p151: CAD file, 2023-03-15]
parts/export/case/right_side_case.3mf
133.1 x 186.1 x 17.0 mm
