thpoll83/PolyKybd/parts/export/keycap_stem/keycap_stem_revAlpha_1U_R1_10p.stl

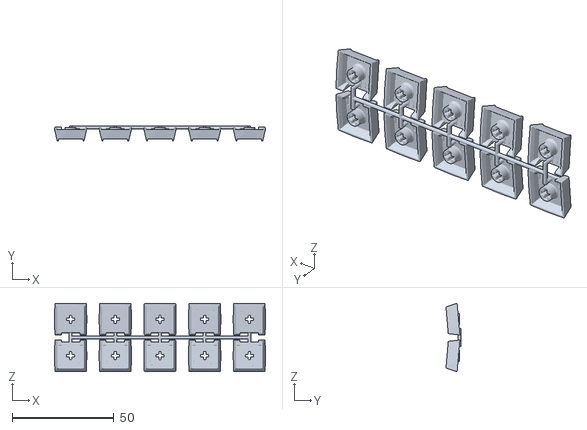
[picture p152: CAD file, 2026-08-18]
parts/export/keycap_stem/keycap_stem_revAlpha_1U_R1_10p.stl
103.9 x 7.45 x 33.7
