thpoll83/PolyKybd/parts/export/keycap_stem/keycap_stem_revAlpha_1U_S5_10p.stl

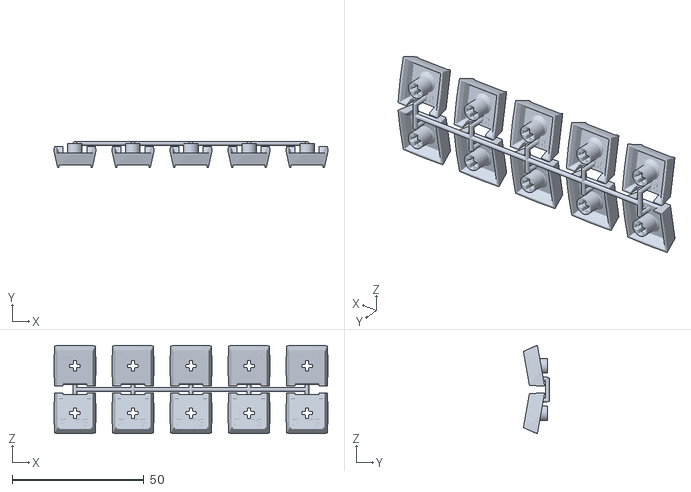
[picture p153: CAD file, 2026-08-16]
parts/export/keycap_stem/keycap_stem_revAlpha_1U_S5_10p.stl
103.9 x 9.96 x 33.5
