thpoll83/PolyKybd/parts/export/keycap_stem/keycap_stem_revAlpha_1U25_S5_10p.stl

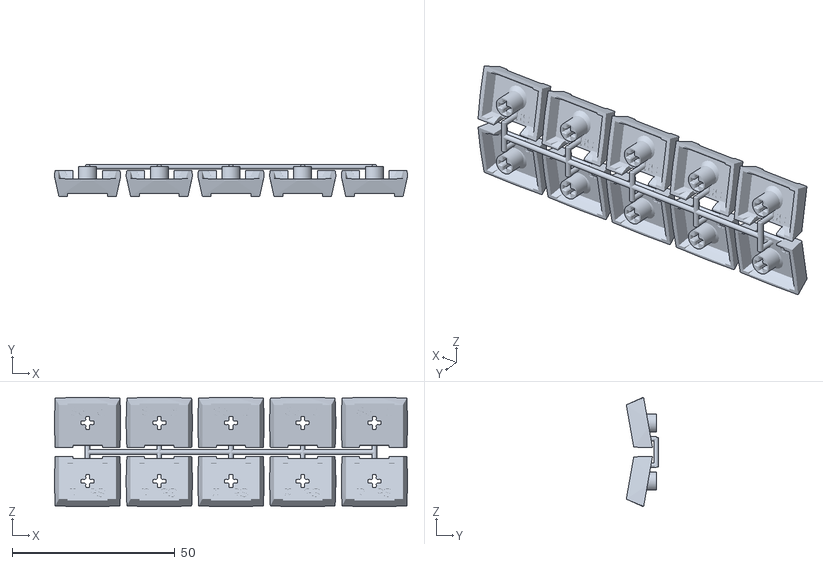
[picture p154: CAD file, 2026-08-16]
parts/export/keycap_stem/keycap_stem_revAlpha_1U25_S5_10p.stl
108.3 x 9.96 x 33.5
