thpoll83/PolyKybd/parts/export/keycap_stem/keycap_stem_revAlpha_1U_S_10p.stl

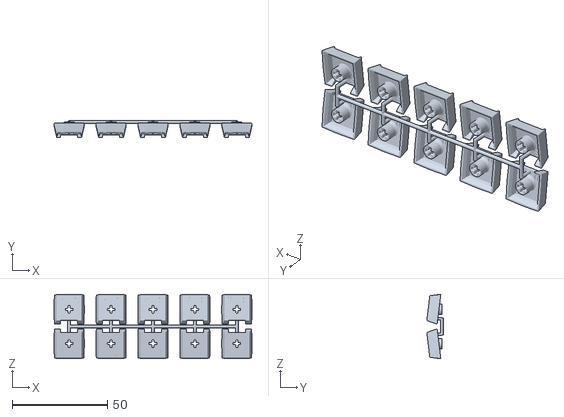
[picture p155: CAD file, 2026-06-16]
parts/export/keycap_stem/keycap_stem_revAlpha_1U_S_10p.stl
103.9 x 8.66 x 33.7
