thpoll83/PolyKybd/parts/export/keycap_stem/keycap_stem_revAlpha_1U25_S_10p.stl

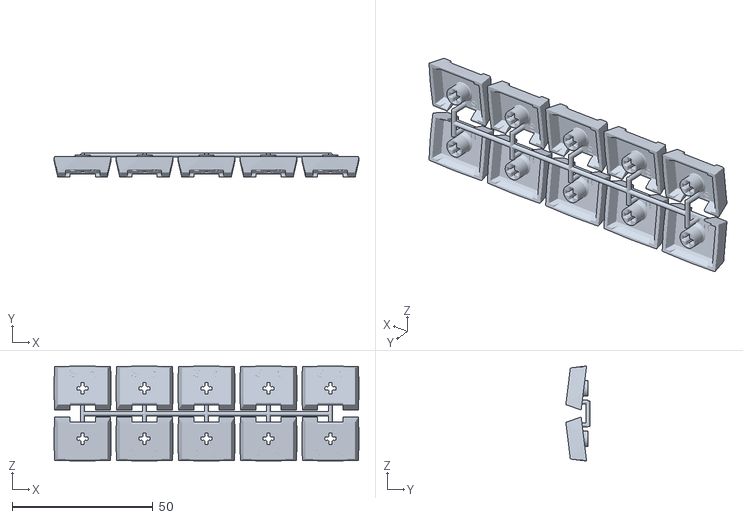
[picture p156: CAD file, 2026-06-16]
parts/export/keycap_stem/keycap_stem_revAlpha_1U25_S_10p.stl
108.3 x 8.66 x 33.7
