thpoll83/PolyKybd/parts/export/keycap_stem/keywitch_cap.stl

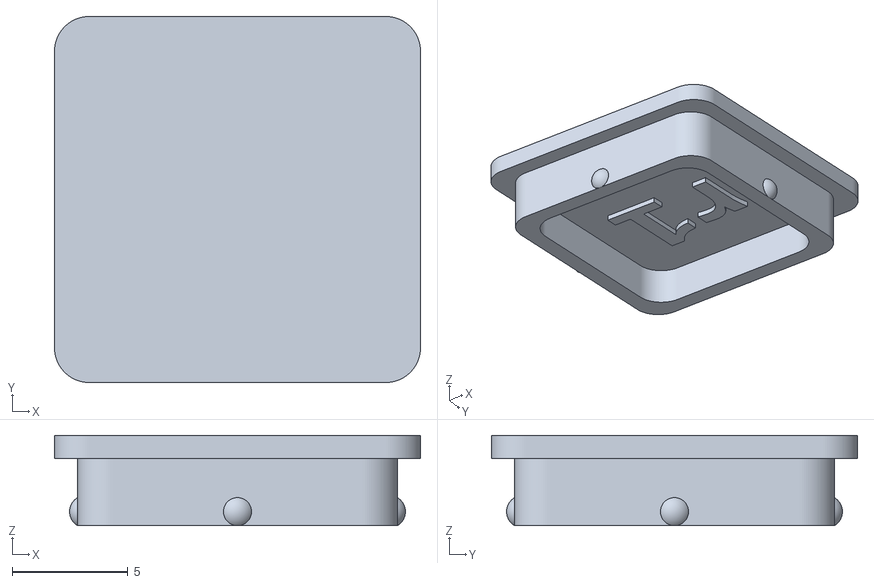
[picture p157: CAD file, 2023-06-22]
parts/export/keycap_stem/keywitch_cap.stl
15.8 x 15.8 x 3.89
