thpoll83/PolyKybd/images/high_res/left_resin_prints.jpg

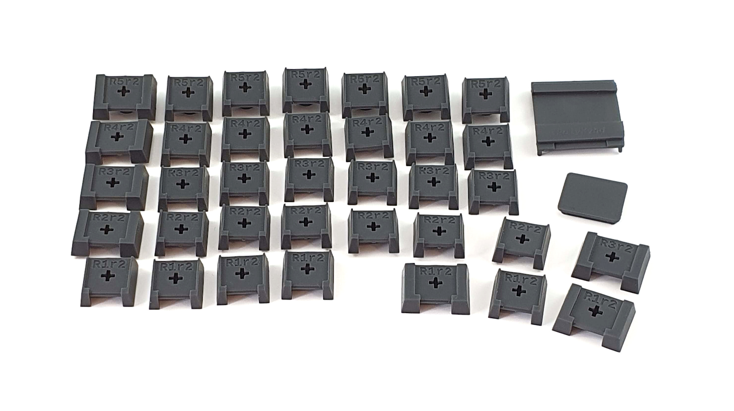
images/high_res/left_resin_prints.jpg
