thpoll83/PolyKybd/parts/case/step/compare.png

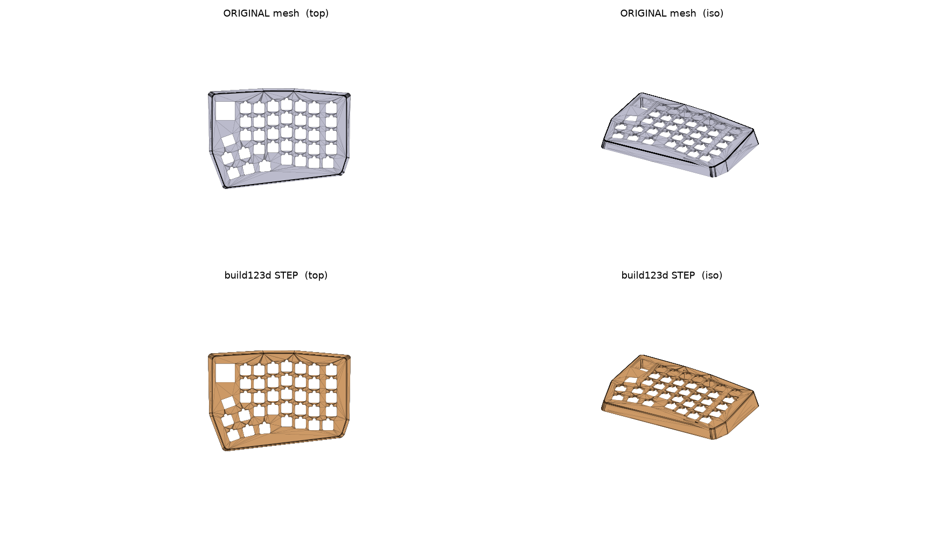
parts/case/step/compare.png
