thpoll83/PolyKybd/RoHS/schematics/poly_kybd_split72_right.pdf

# File: SSD1306_TO_SPI.kicad_sch VCC GND B_IN

# File: SSD1306_TO_SPI.kicad_sch SDIN

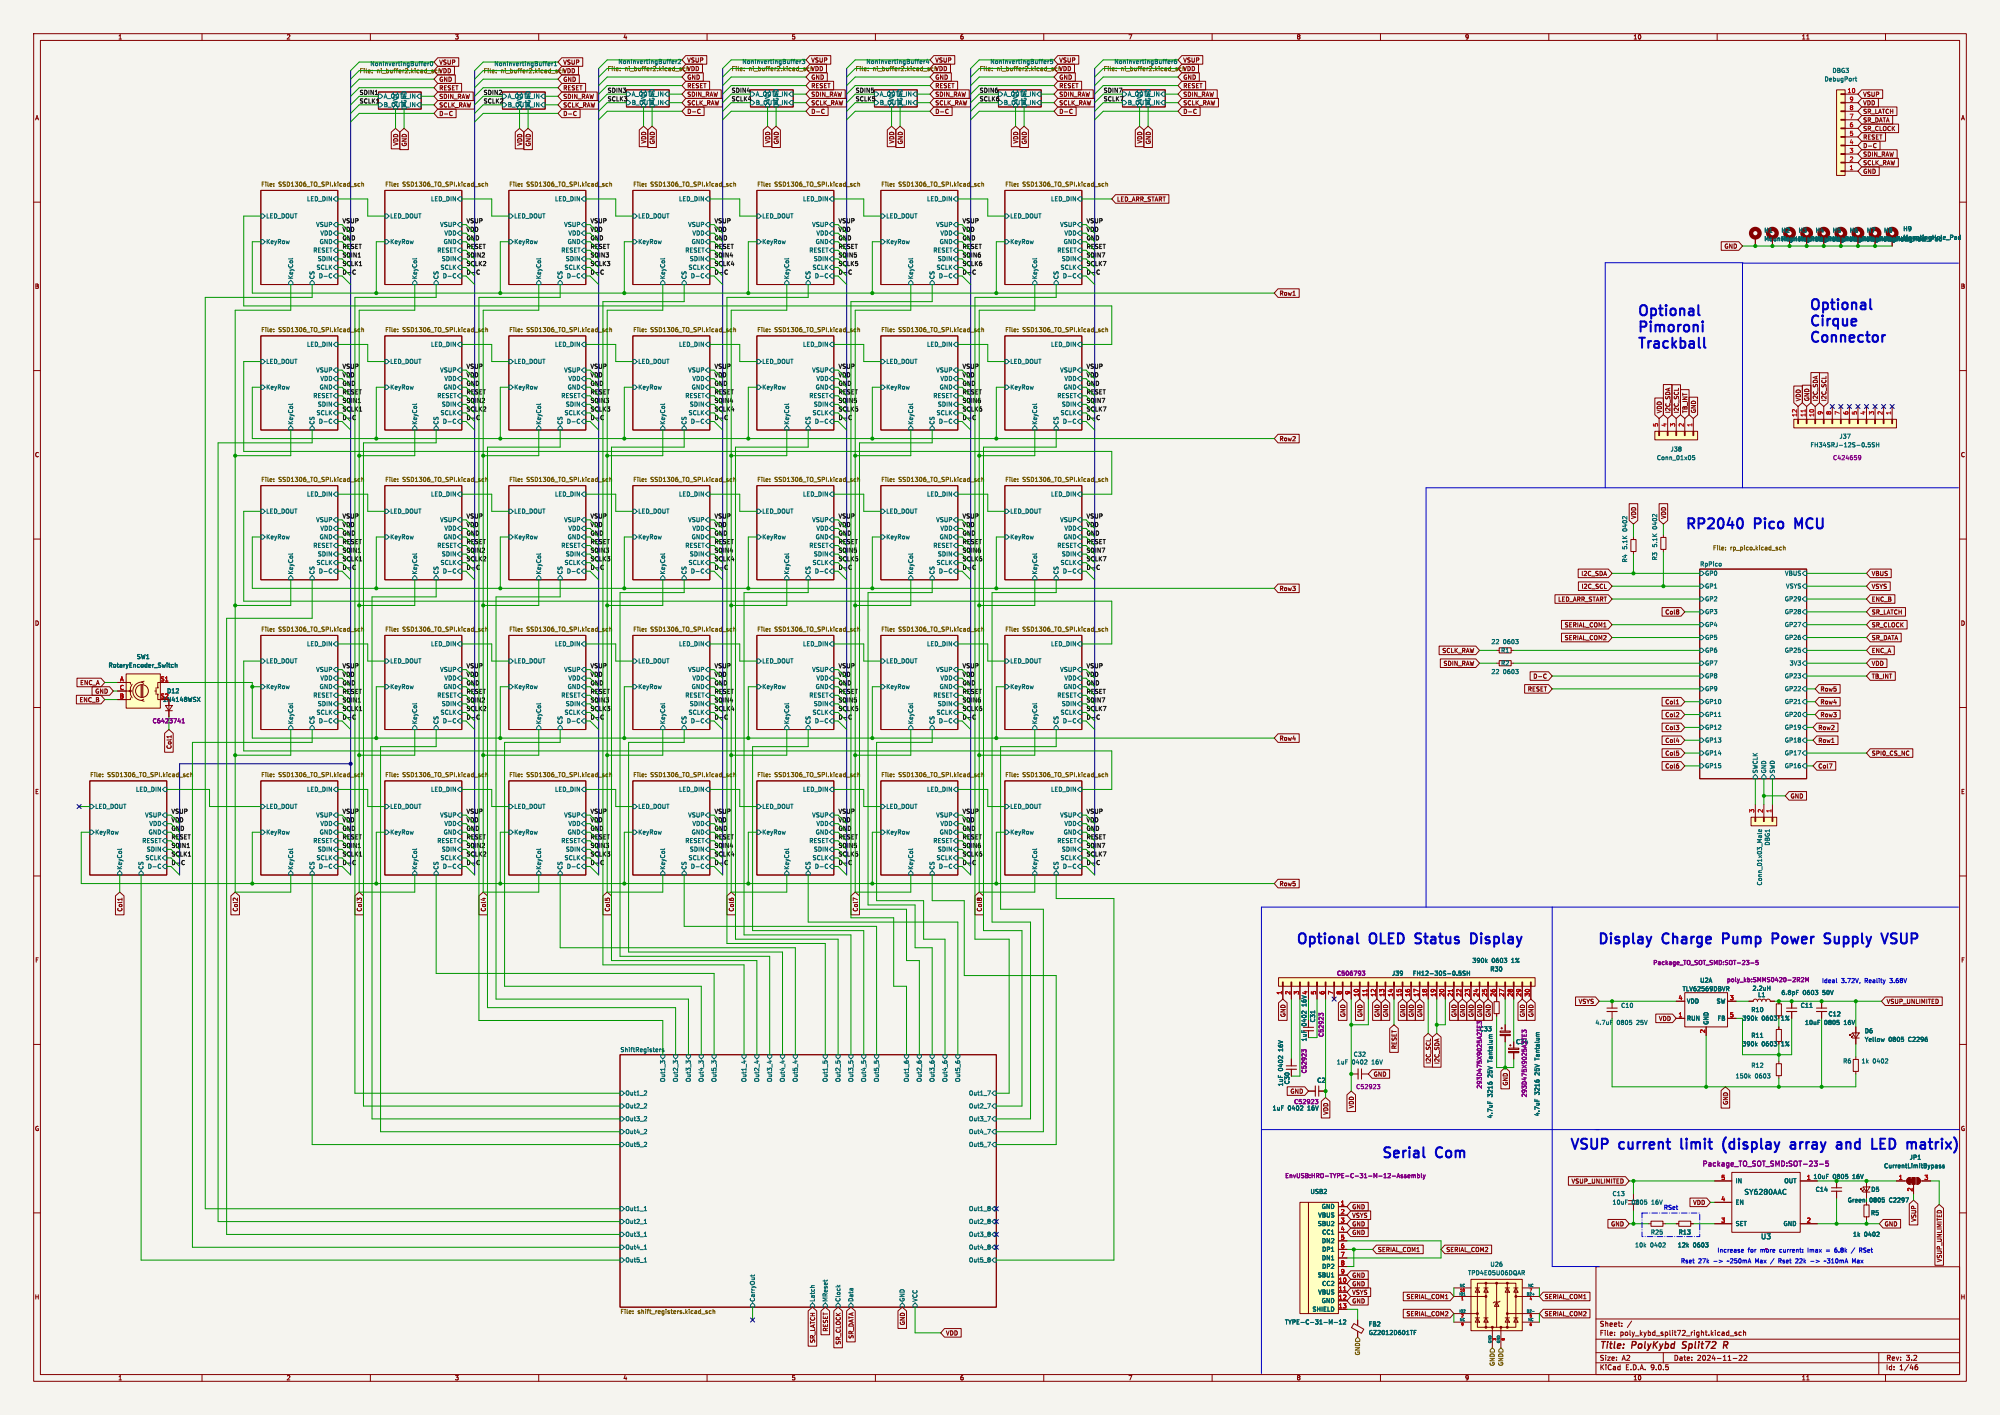
[picture p171: page 1]

Ideal 3.72V, Reality 3.68V RP2040 Pico MCU

Optional OLED Status Display

RSet Display Charge Pump Power Supply VSUP
TLV62569DBVR

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

USB2 TYPE-C-31-M-12 EnvUSB:HRO-TYPE-C-31-M-12-Assembly GND

https://www.lcsc.com/datasheet/lcsc_datasheet_1810121532_Silergy-Corp-SY6280AAC_C55136.pdf
