thpoll83/PolyKybd/RoHS/2304140030_JUSHUO-AFC42-S14FMA-1H_C466533.pdf

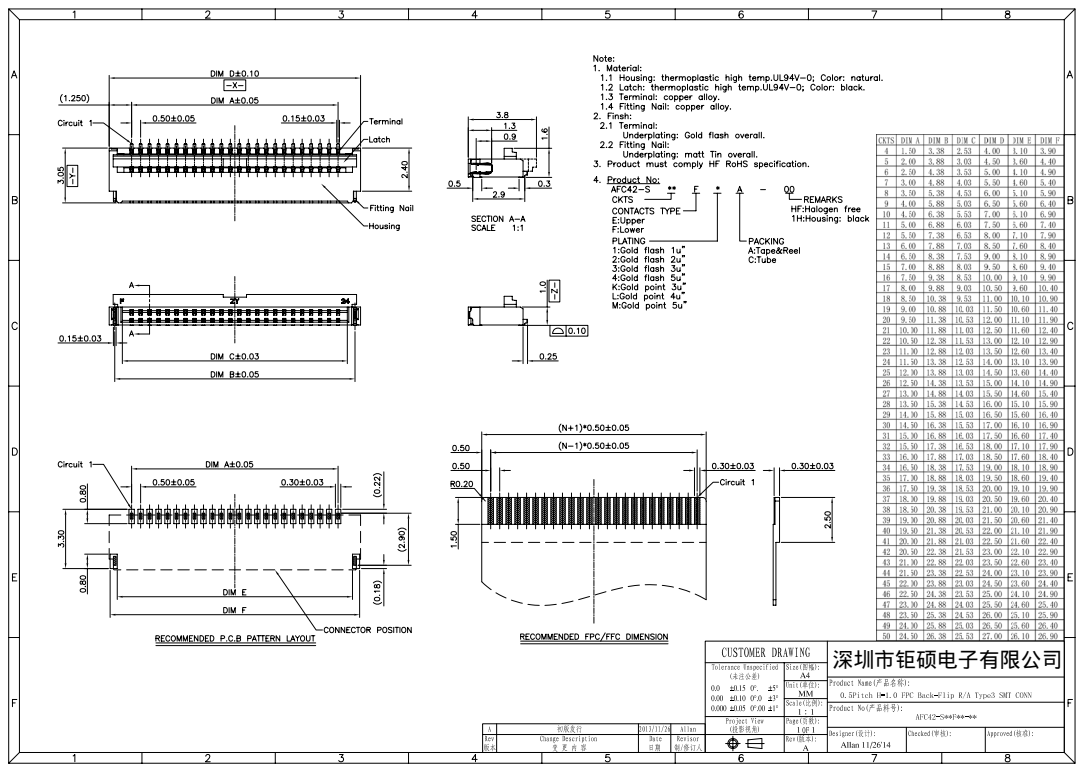
[picture p172: page 1]
深圳市钜硕电子有限公司
