thpoll83/PolyKybd/RoHS/2410010003_Korean-Hroparts-Elec-TYPE-C-31-M-12_C165948.pdf

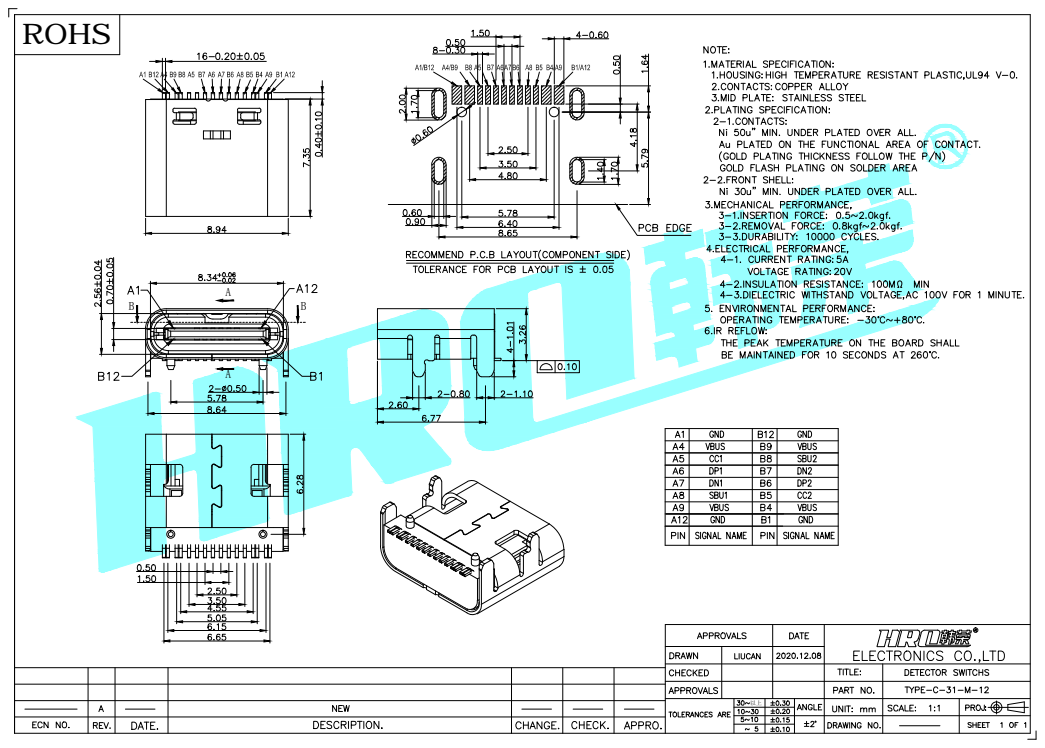
[picture p173: page 1]
